Avik127/RDNT/website/img/slideshow/477grp18.jpg

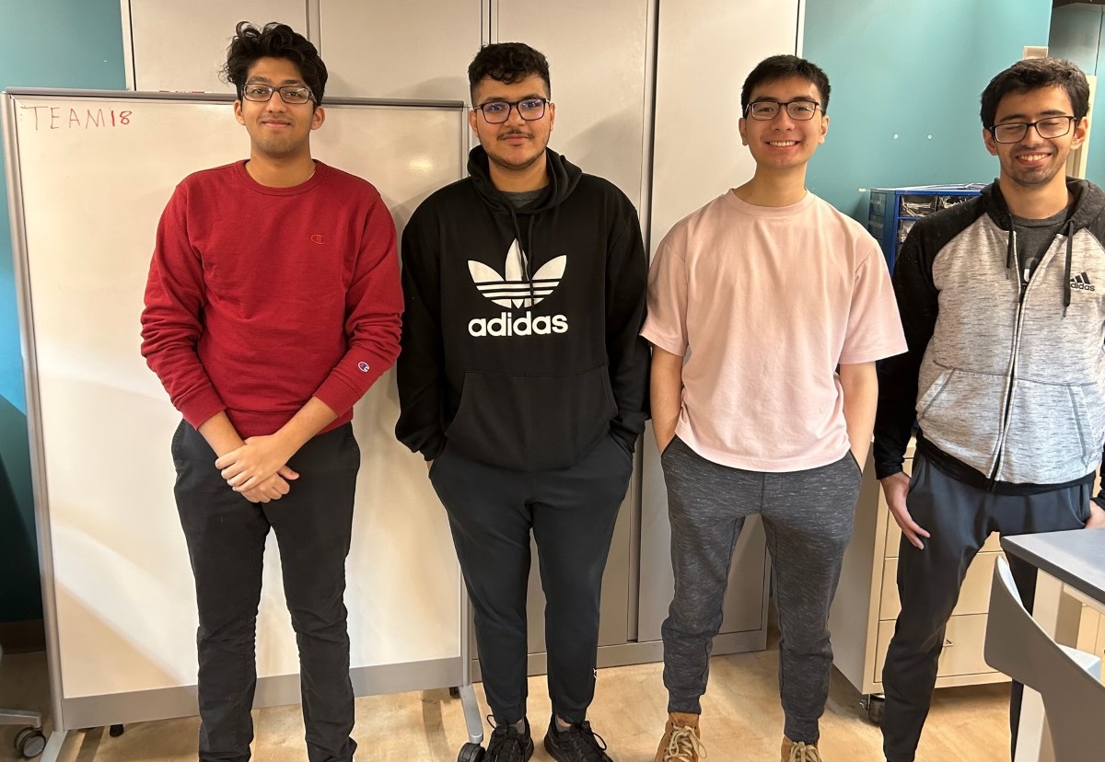
website/img/slideshow/477grp18.jpg
