Avik127/RDNT/website/img/slideshow/team_at_work.jpg

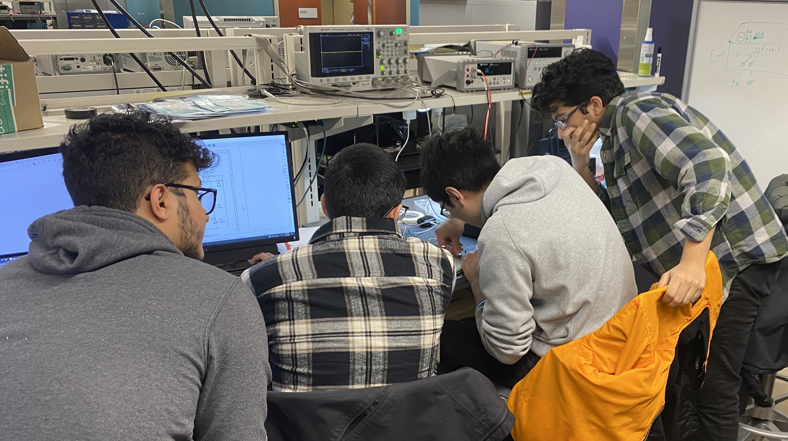
website/img/slideshow/team_at_work.jpg
