Avik127/RDNT/website/img/slideshow/team_done.jpg

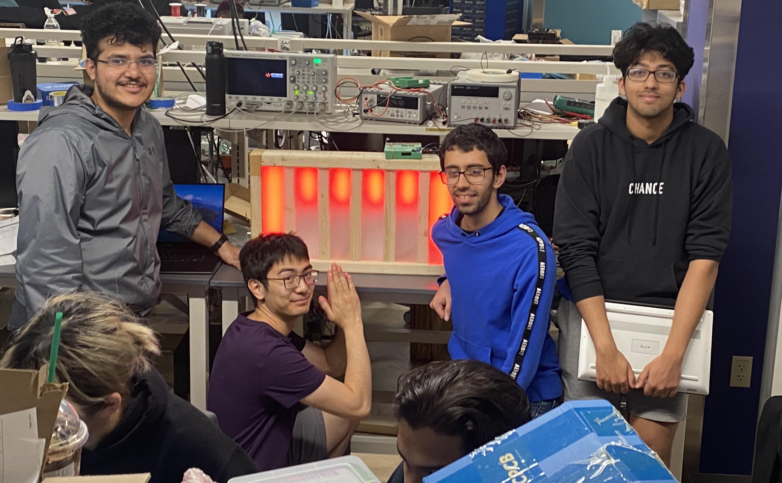
website/img/slideshow/team_done.jpg
