Avik127/RDNT/website/Team/img/avik.jpg

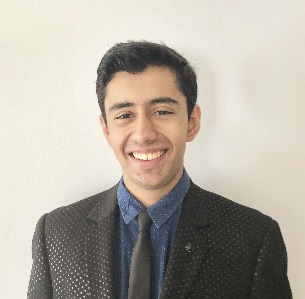
website/Team/img/avik.jpg
