Avik127/RDNT/website/Team/img/graeme.jpg

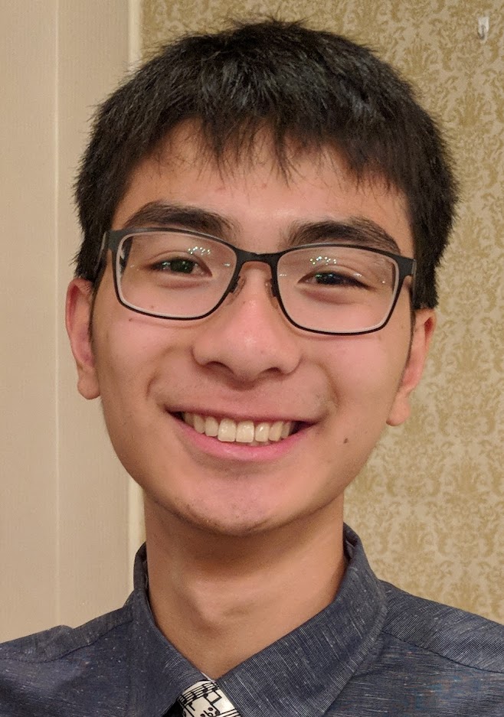
website/Team/img/graeme.jpg
