Avik127/RDNT/website/Team/progress/progress1pics/amp_voltage.jpg

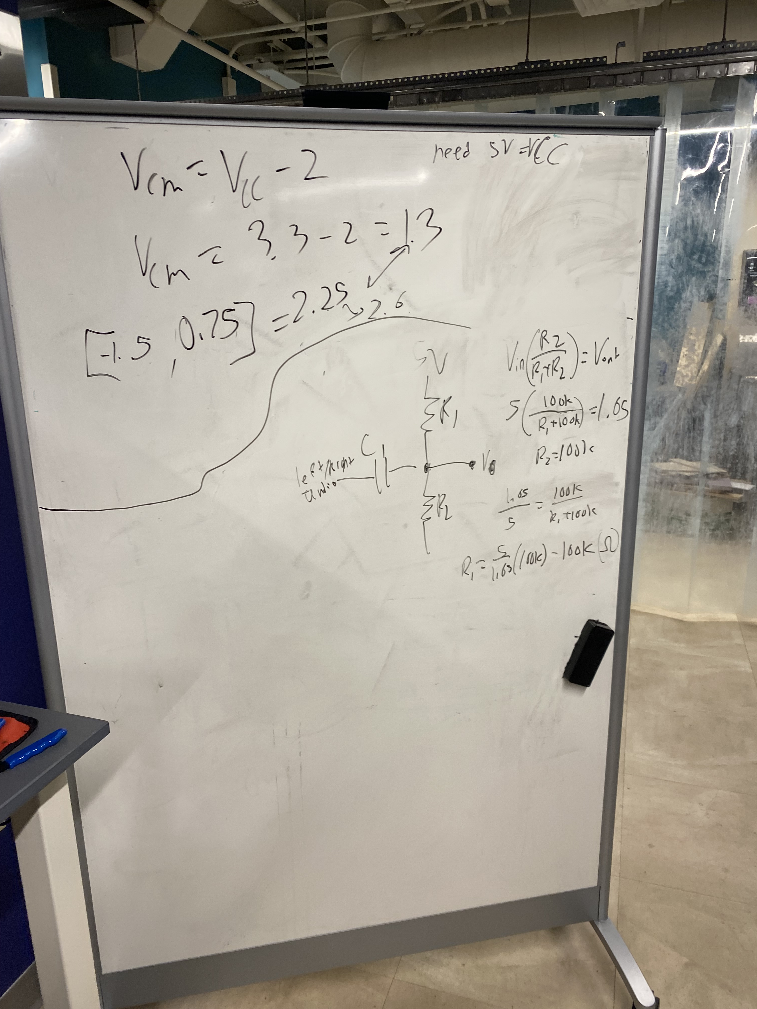
website/Team/progress/progress1pics/amp_voltage.jpg
