Avik127/RDNT/website/Team/progress/progress1pics/appdraft1.jpg

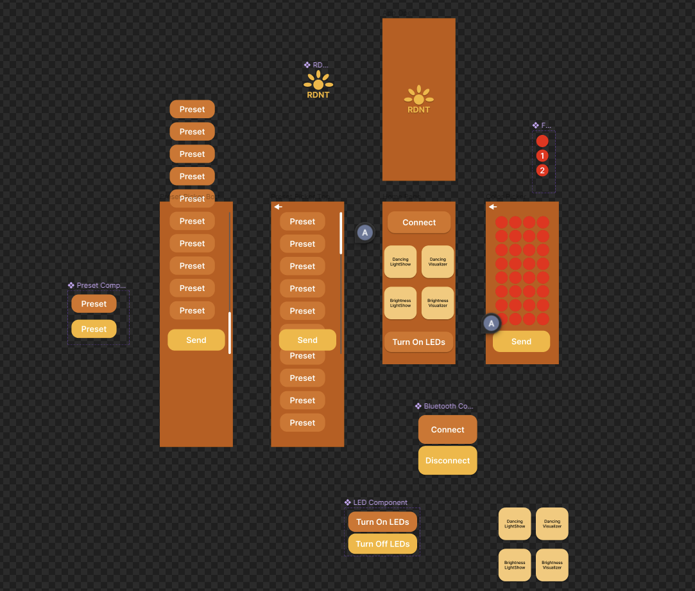
website/Team/progress/progress1pics/appdraft1.jpg
