Avik127/RDNT/website/Team/progress/progress1pics/AUX_circuit.jpg

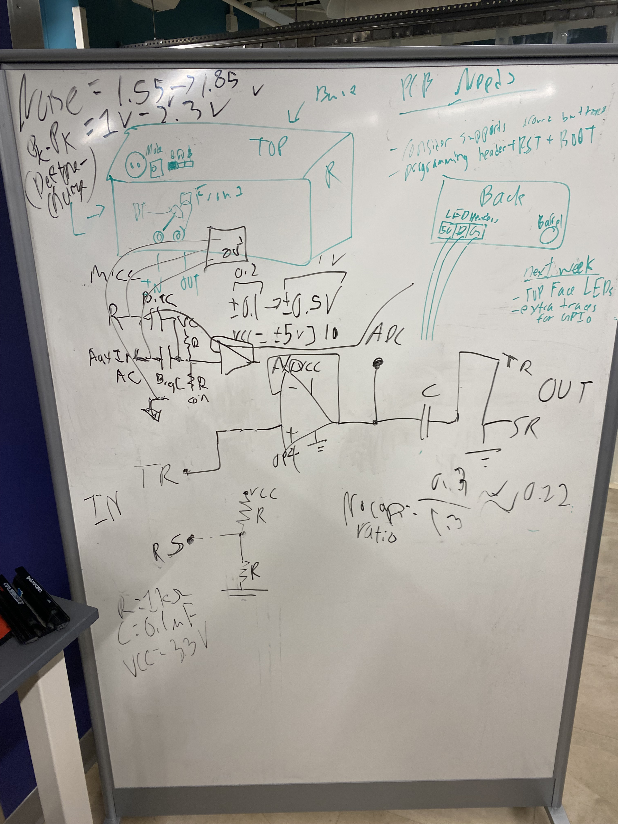
website/Team/progress/progress1pics/AUX_circuit.jpg
