Avik127/RDNT/website/Team/progress/progress1pics/desmoscalc.jpg

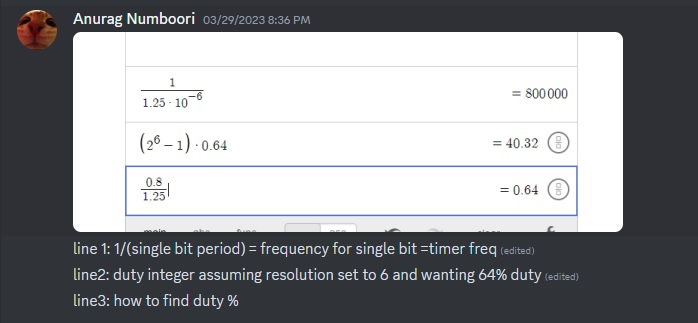
website/Team/progress/progress1pics/desmoscalc.jpg
