Avik127/RDNT/website/Team/progress/progress1pics/flashing.gif

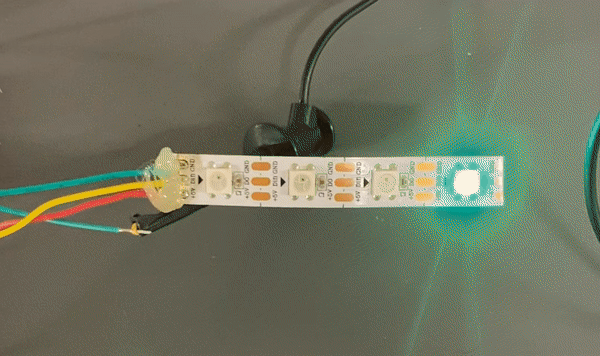
website/Team/progress/progress1pics/flashing.gif
