Avik127/RDNT/website/Team/progress/progress1pics/gain10.jpg

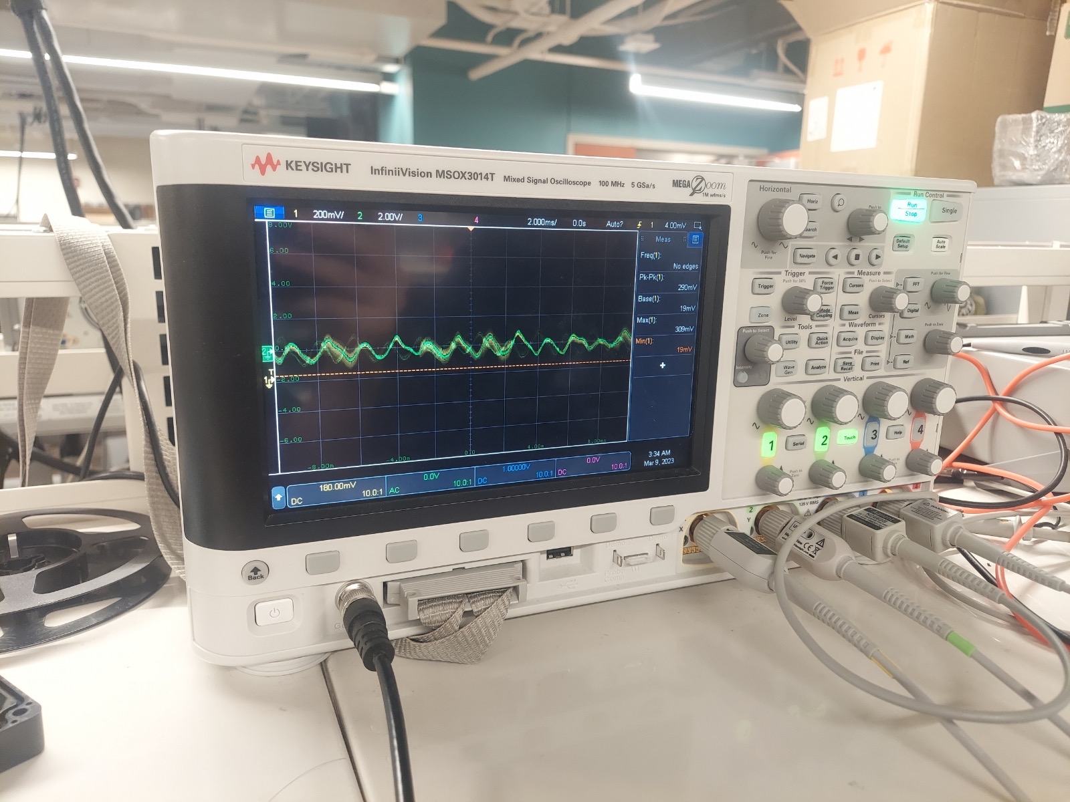
website/Team/progress/progress1pics/gain10.jpg
