Avik127/RDNT/website/Team/progress/progress1pics/GaussianDistribution.png

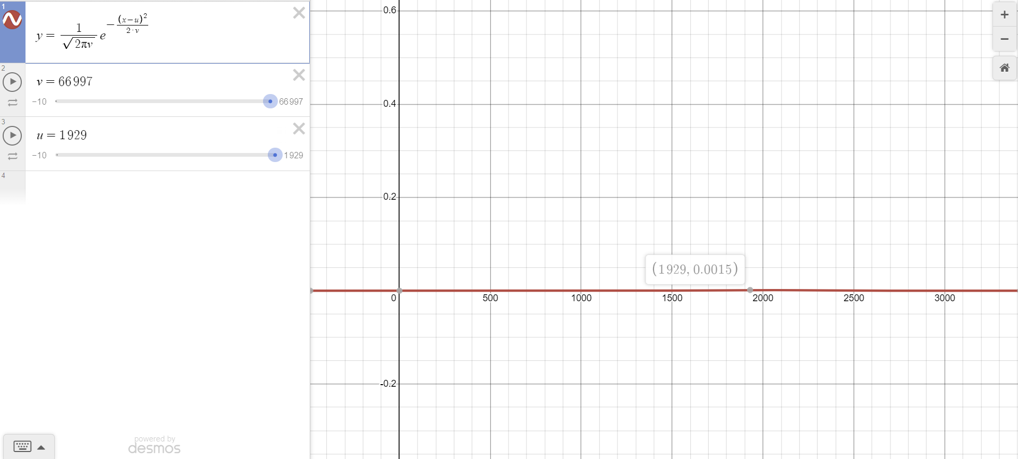
website/Team/progress/progress1pics/GaussianDistribution.png
