Avik127/RDNT/website/Team/progress/progress1pics/glue.jpg

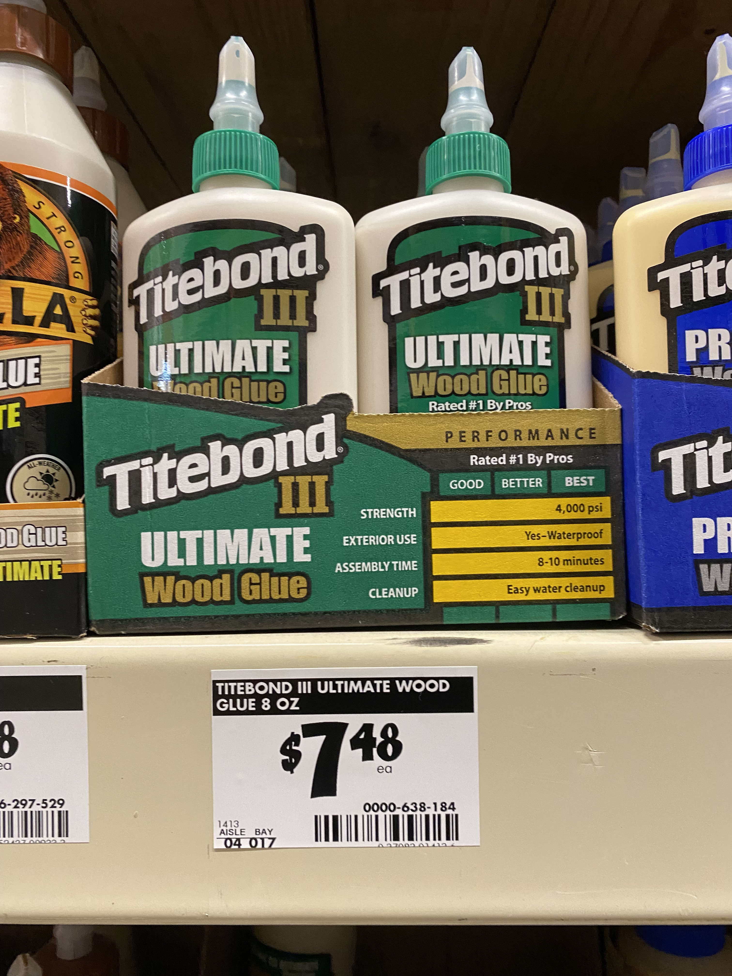
website/Team/progress/progress1pics/glue.jpg
