Avik127/RDNT/website/Team/progress/progress1pics/gpio.jpg

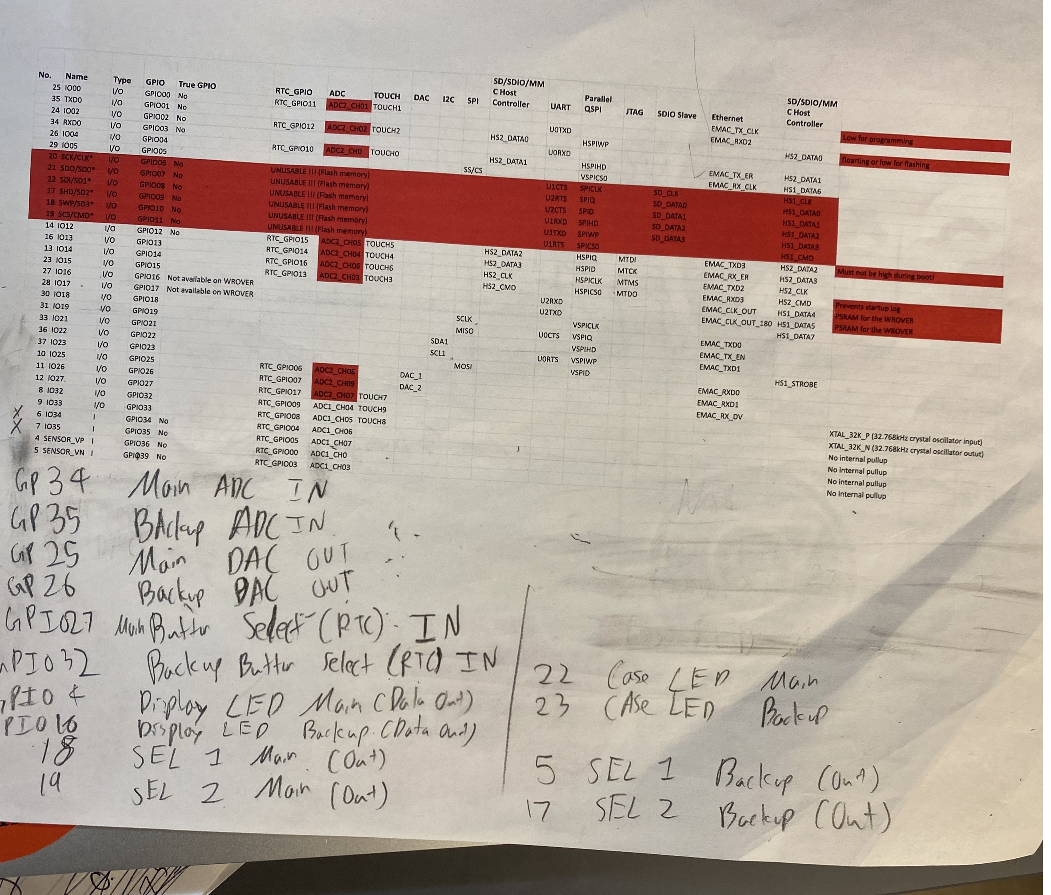
website/Team/progress/progress1pics/gpio.jpg
