Avik127/RDNT/website/Team/progress/progress1pics/IMG_4288.jpg

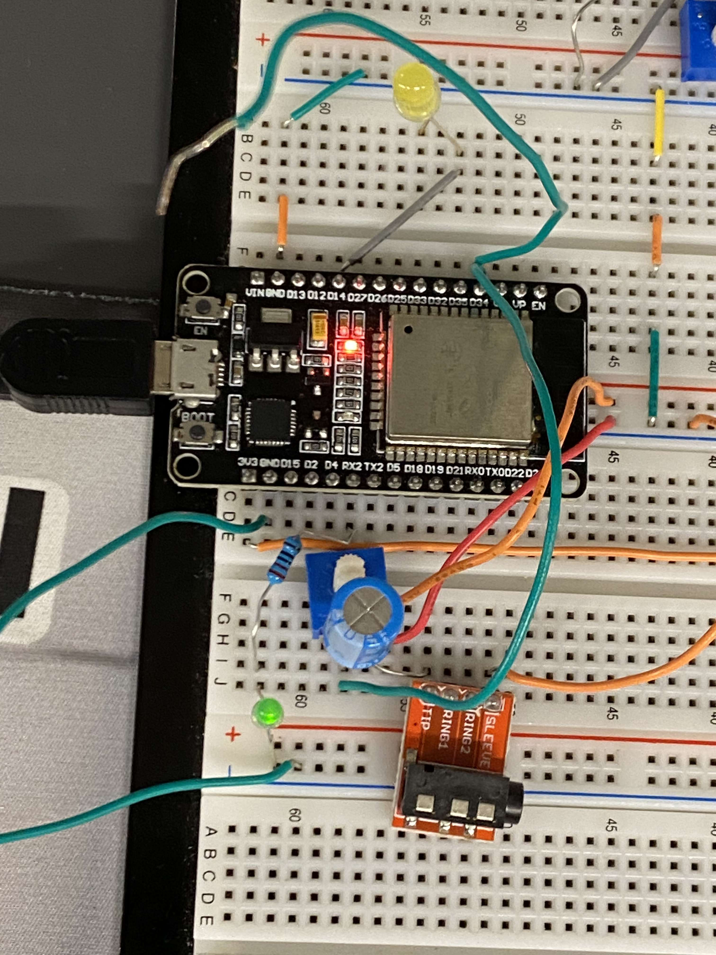
website/Team/progress/progress1pics/IMG_4288.jpg
