Avik127/RDNT/website/Team/progress/progress1pics/multi_color.jpg

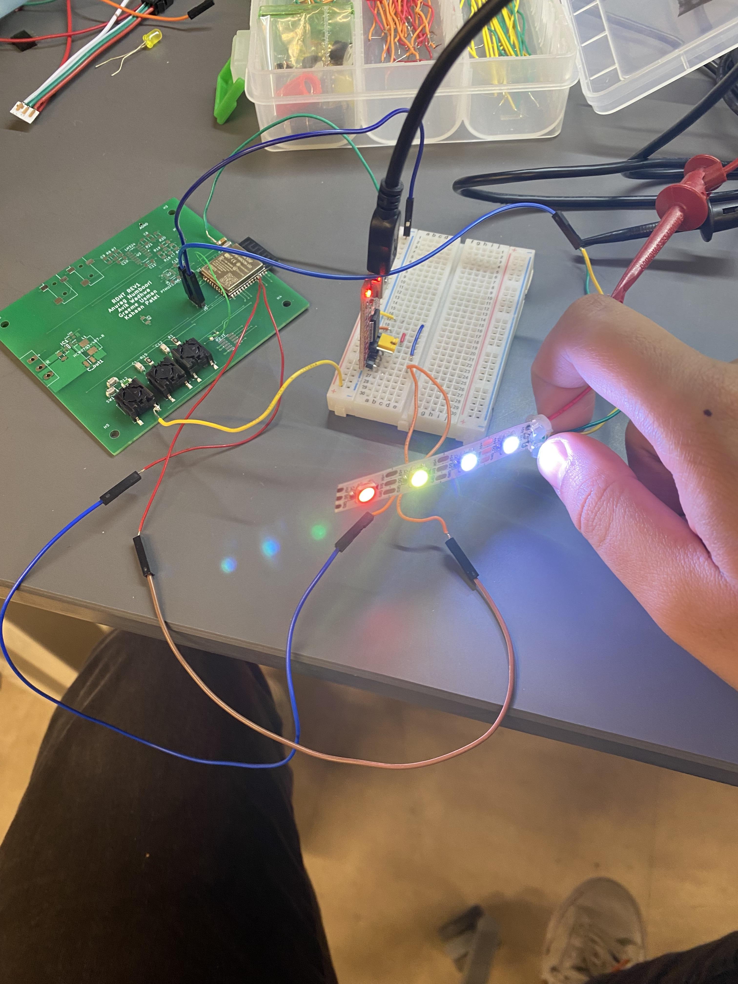
website/Team/progress/progress1pics/multi_color.jpg
