Avik127/RDNT/website/Team/progress/progress1pics/pcb_white.jpg

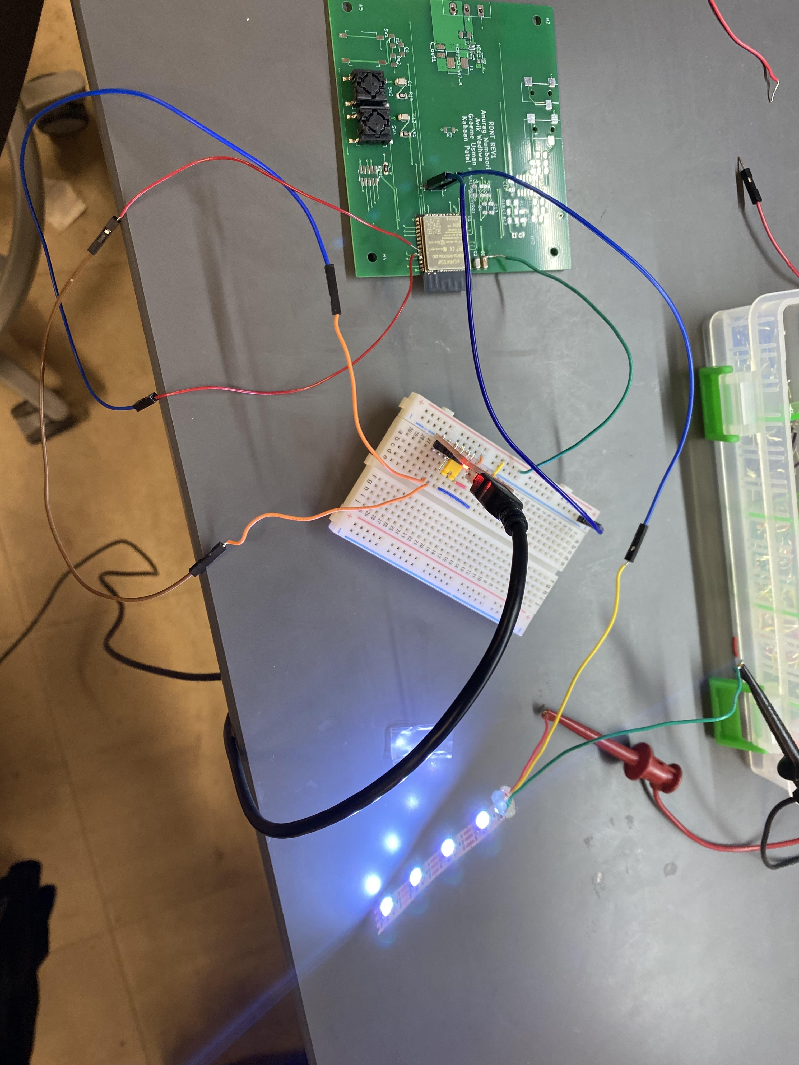
website/Team/progress/progress1pics/pcb_white.jpg
