Avik127/RDNT/website/Team/progress/progress1pics/pwm.jpg

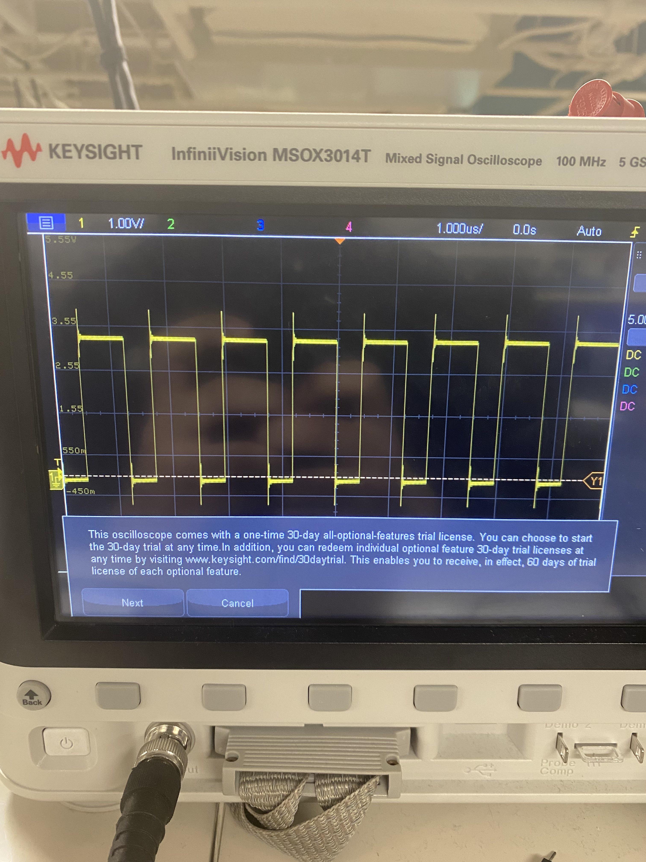
website/Team/progress/progress1pics/pwm.jpg
