Avik127/RDNT/website/Team/progress/progress1pics/red_flashing.gif

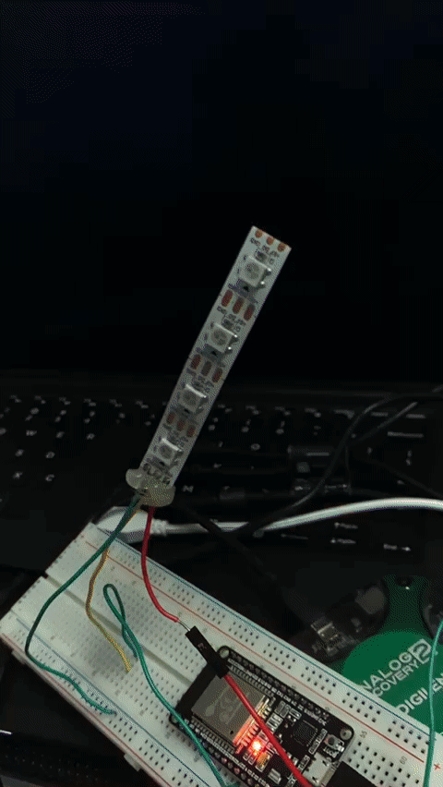
website/Team/progress/progress1pics/red_flashing.gif
