Avik127/RDNT/website/Team/progress/progress1pics/stain.jpg

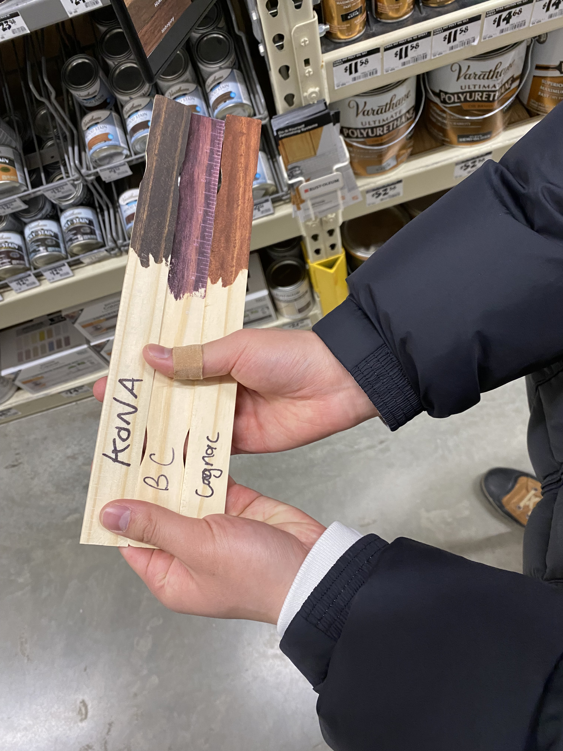
website/Team/progress/progress1pics/stain.jpg
