Avik127/RDNT/website/Team/progress/progress1pics/varnish.jpg

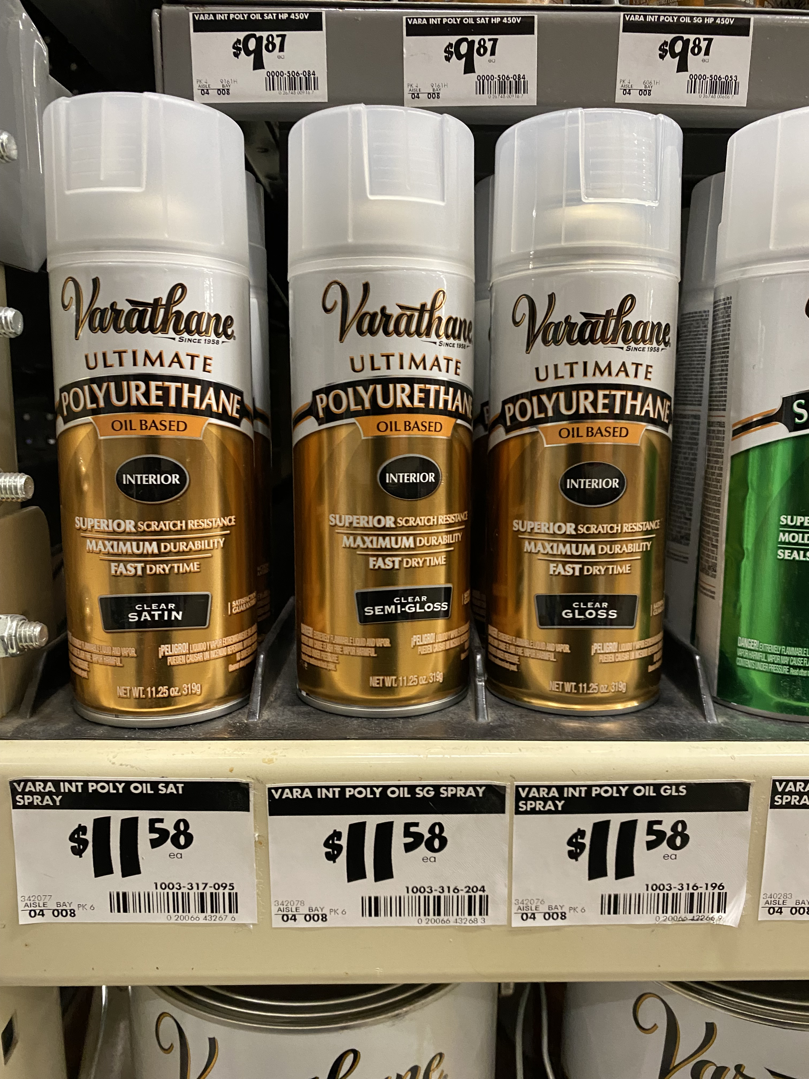
website/Team/progress/progress1pics/varnish.jpg
