Avik127/RDNT/website/Team/progress/progress1pics/whitelights.jpg

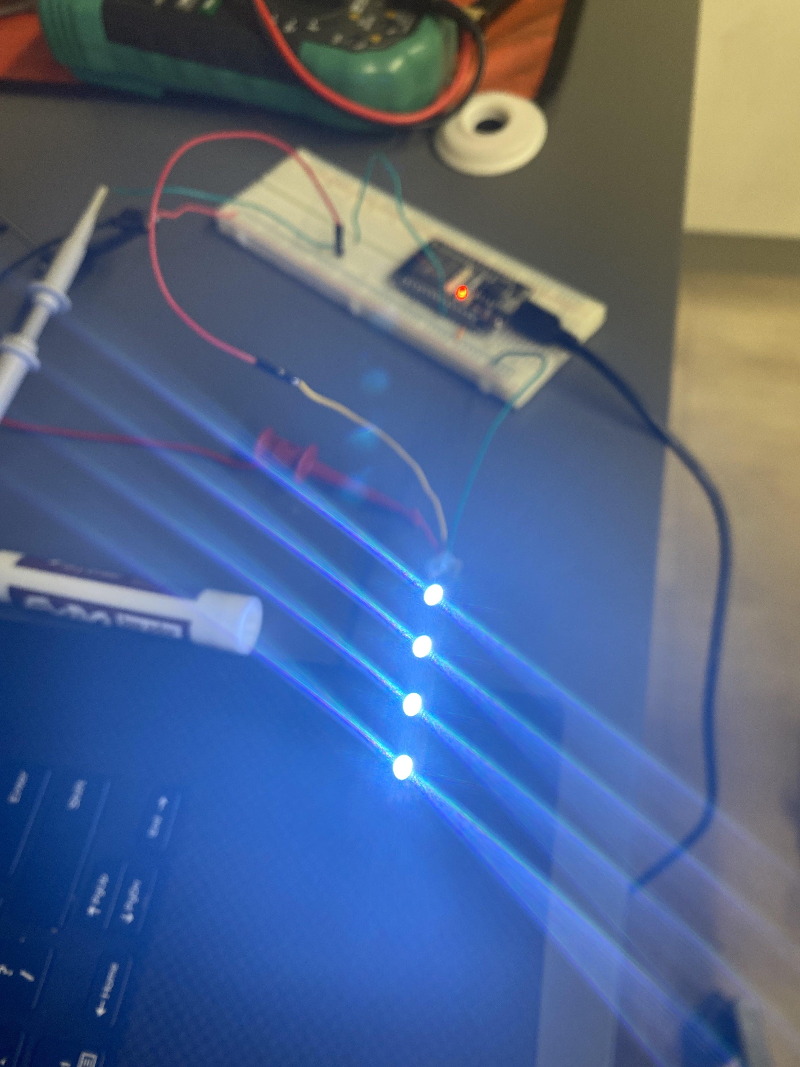
website/Team/progress/progress1pics/whitelights.jpg
