Avik127/RDNT/website/Team/progress/progress1pics/wire_awg.jpg

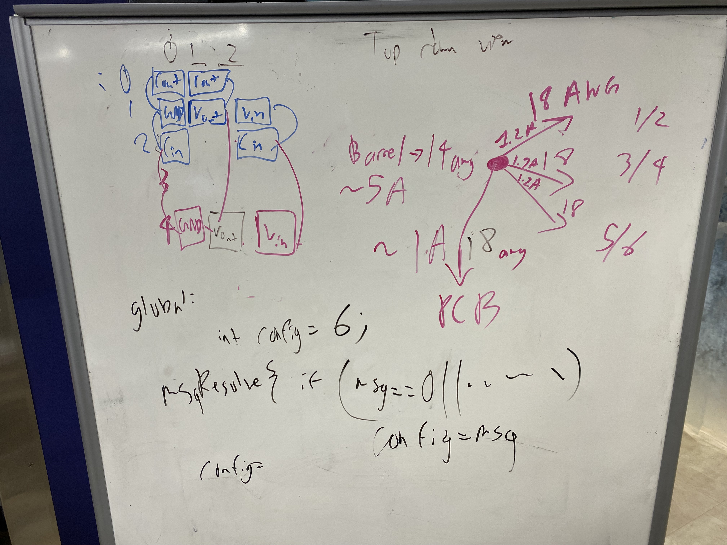
website/Team/progress/progress1pics/wire_awg.jpg
