Avik127/RDNT/website/Team/progress/progress1pics/wood.jpg

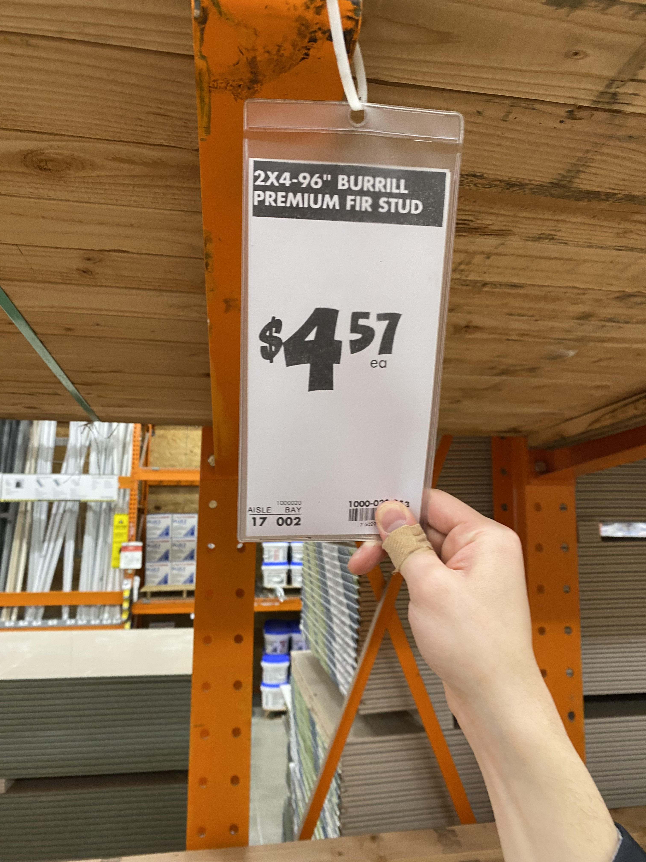
website/Team/progress/progress1pics/wood.jpg
