Avik127/RDNT/website/Team/progress/progress2pics/5V_crisis_averted.jpg

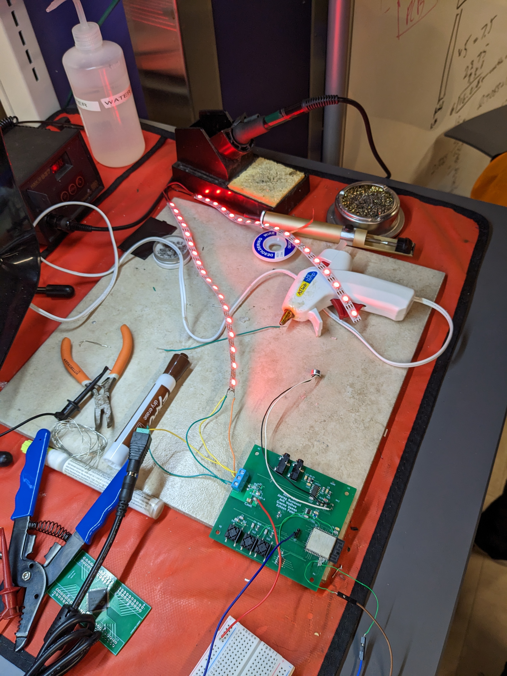
website/Team/progress/progress2pics/5V_crisis_averted.jpg
