Avik127/RDNT/website/Team/progress/progress2pics/acrylic_frosted.jpg

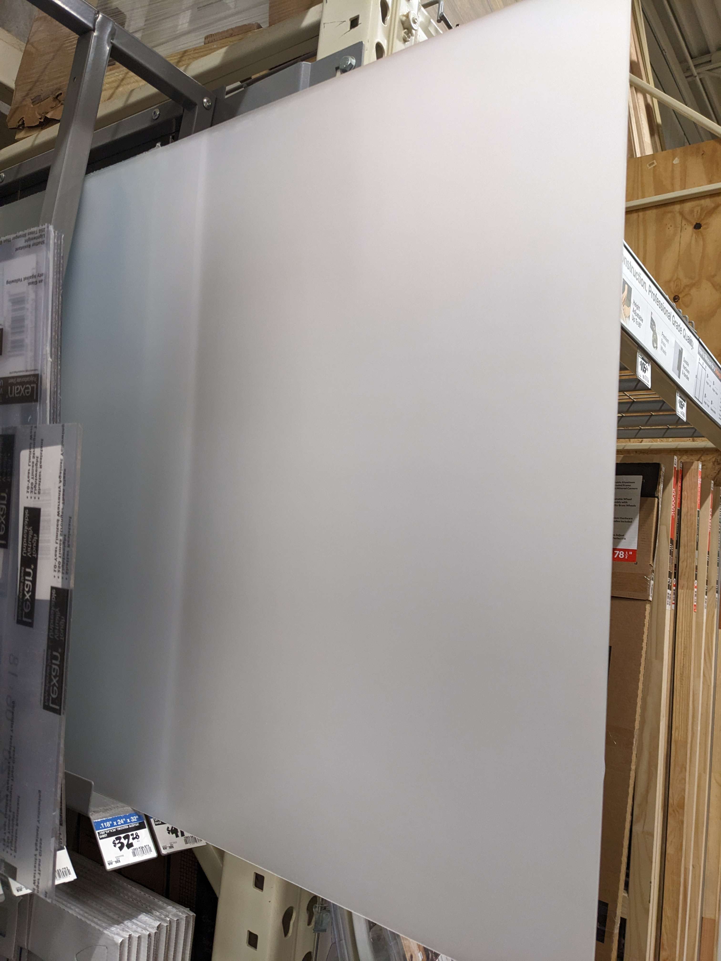
website/Team/progress/progress2pics/acrylic_frosted.jpg
