Avik127/RDNT/website/Team/progress/progress2pics/acrylic_pricetag.jpg

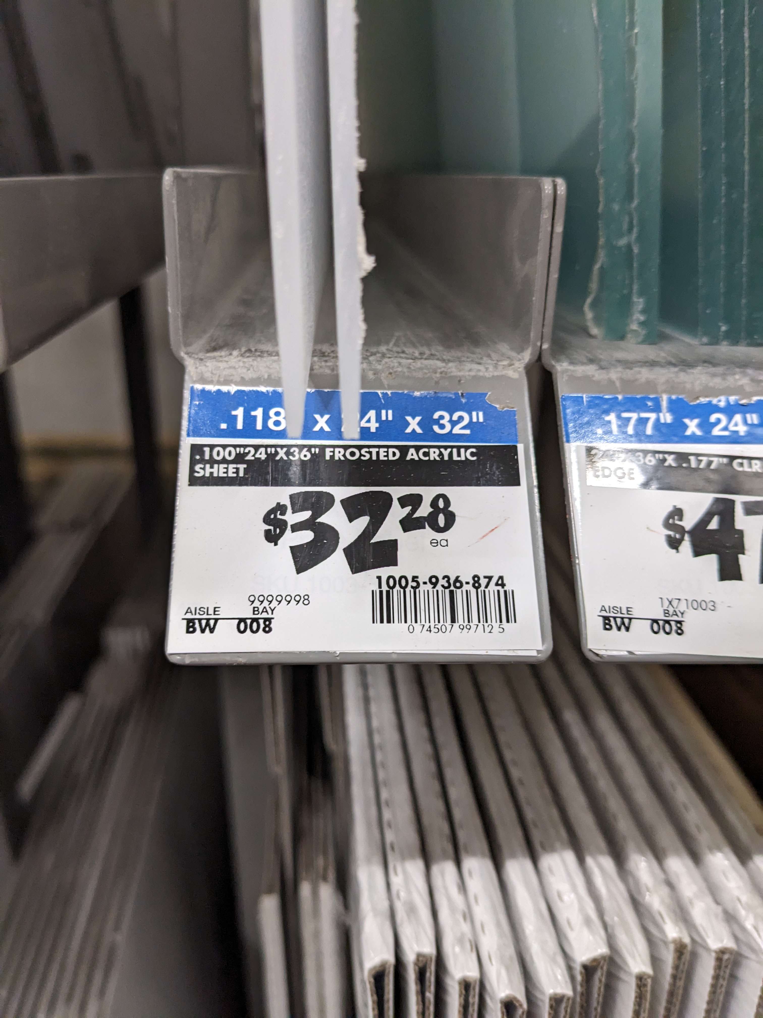
website/Team/progress/progress2pics/acrylic_pricetag.jpg
