Avik127/RDNT/website/Team/progress/progress2pics/AD2_wavegen.jpg

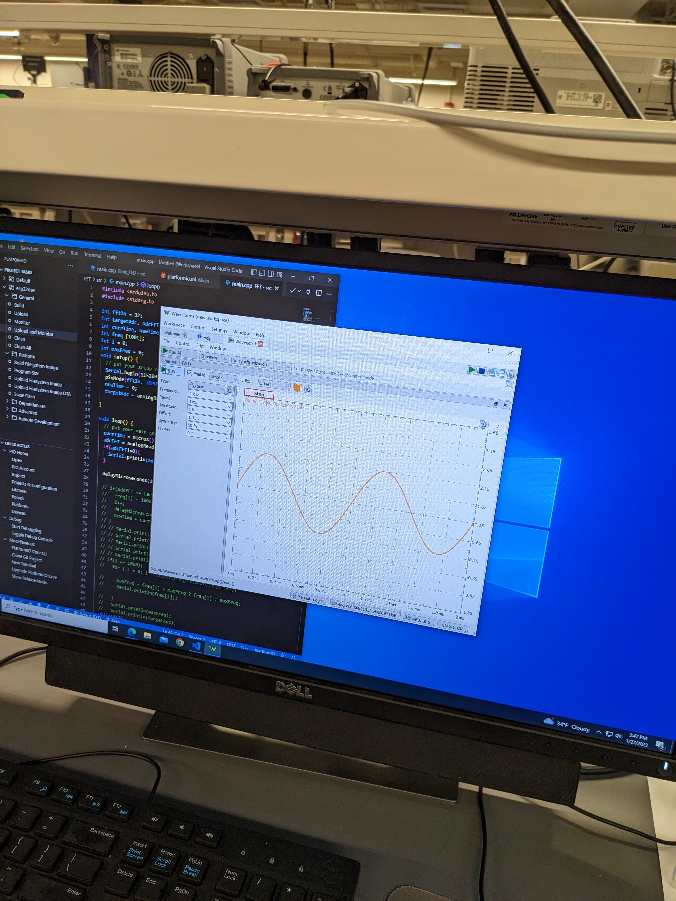
website/Team/progress/progress2pics/AD2_wavegen.jpg
