Avik127/RDNT/website/Team/progress/progress2pics/anu_work.jpg

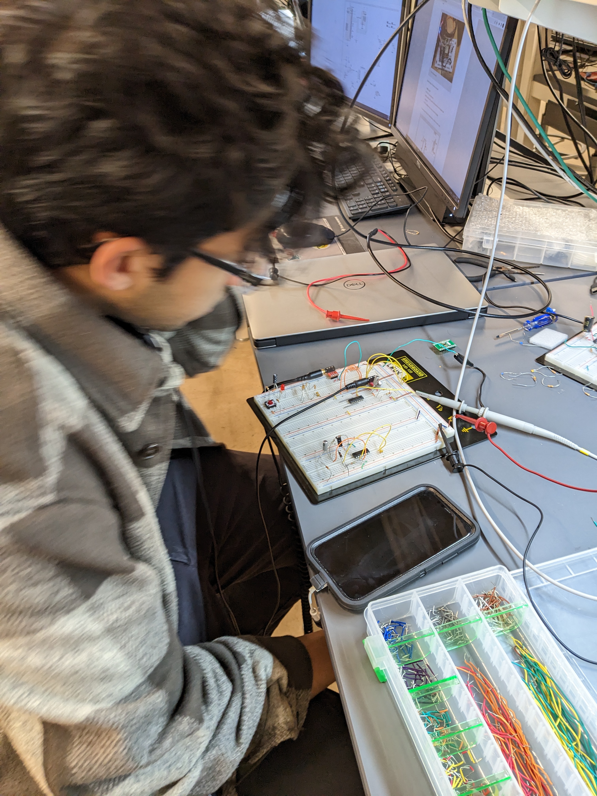
website/Team/progress/progress2pics/anu_work.jpg
