Avik127/RDNT/website/Team/progress/progress2pics/beat_detect.png

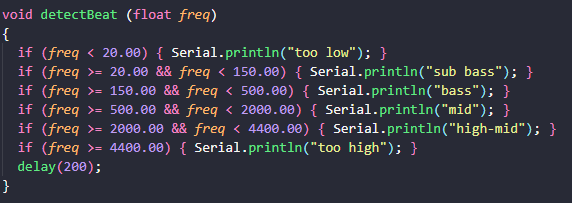
website/Team/progress/progress2pics/beat_detect.png
