Avik127/RDNT/website/Team/progress/progress2pics/button_debounced.jpg

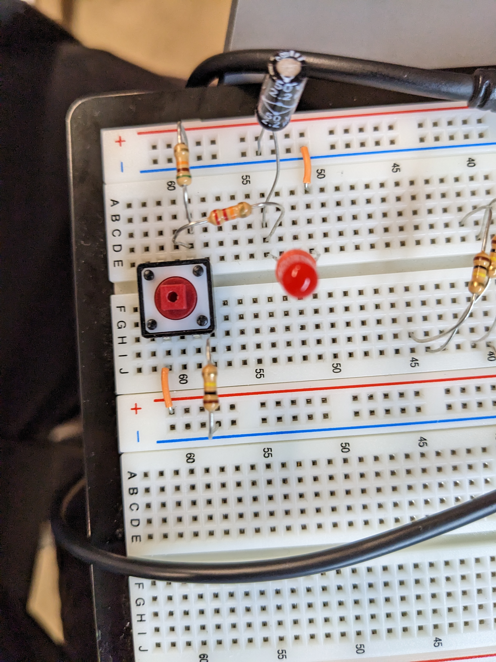
website/Team/progress/progress2pics/button_debounced.jpg
