Avik127/RDNT/website/Team/progress/progress2pics/code_3.26.png

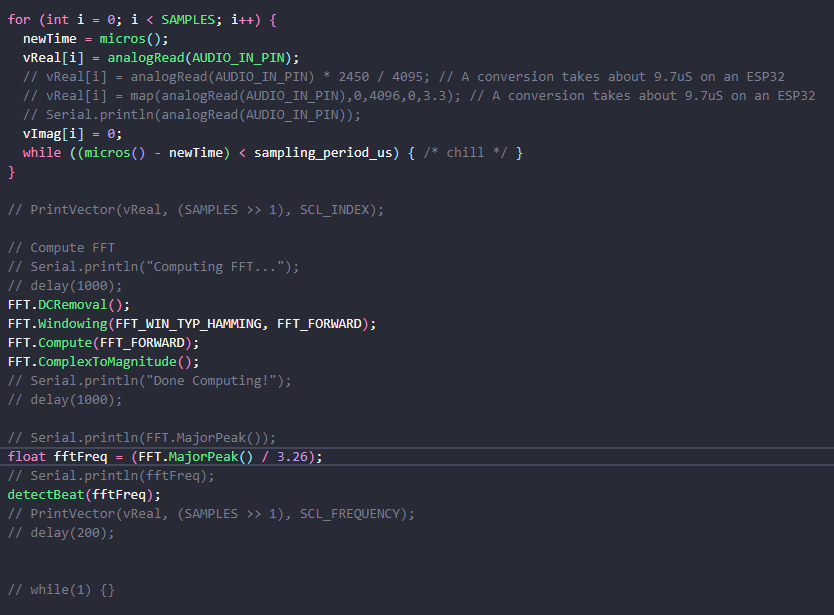
website/Team/progress/progress2pics/code_3.26.png
