Avik127/RDNT/website/Team/progress/progress2pics/epoxy.jpg

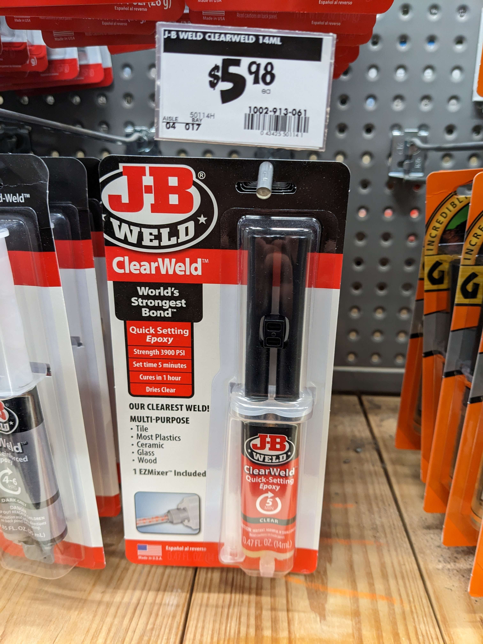
website/Team/progress/progress2pics/epoxy.jpg
