Avik127/RDNT/website/Team/progress/progress2pics/esp_time.jpg

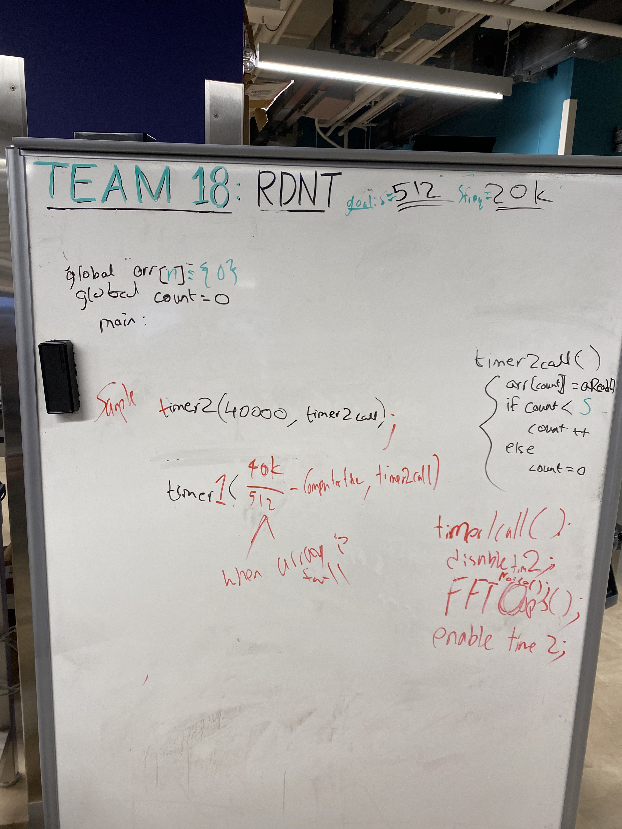
website/Team/progress/progress2pics/esp_time.jpg
