Avik127/RDNT/website/Team/progress/progress2pics/frame_update_thurs.jpg

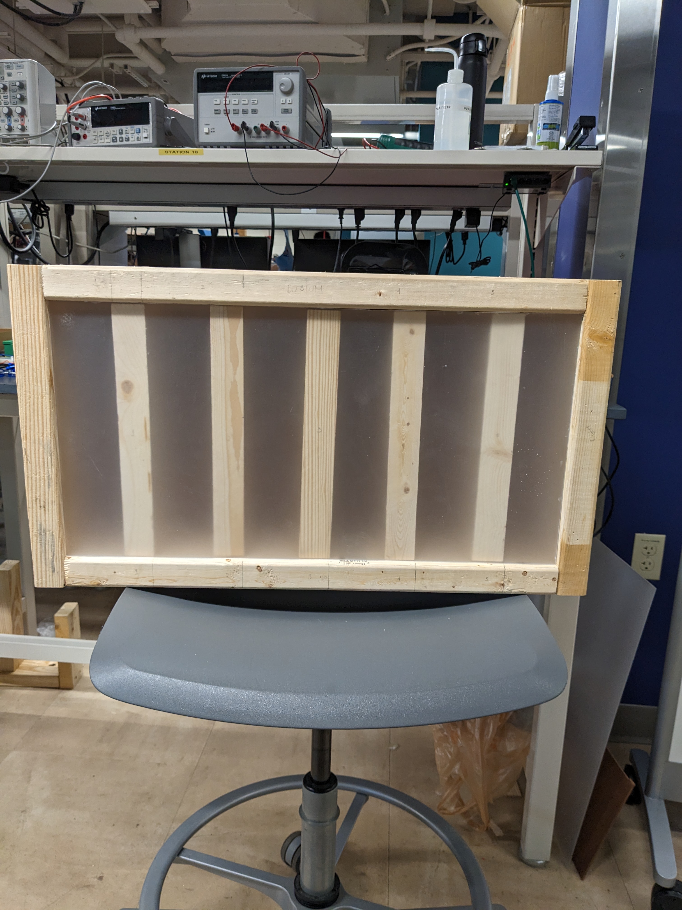
website/Team/progress/progress2pics/frame_update_thurs.jpg
