Avik127/RDNT/website/Team/progress/progress2pics/frame_update_wed.jpg

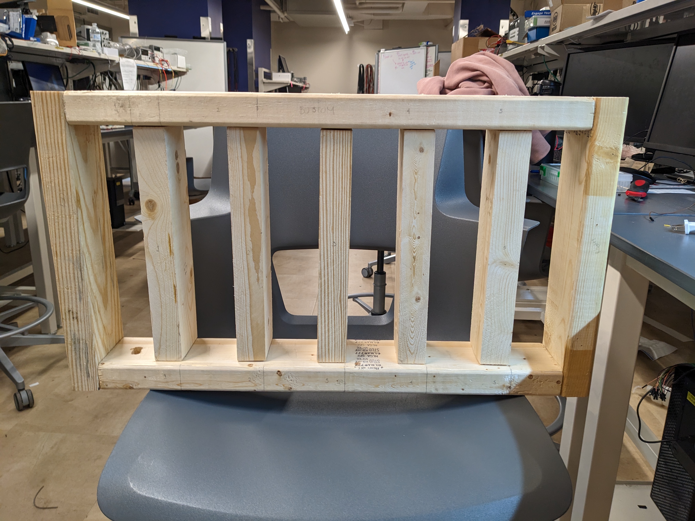
website/Team/progress/progress2pics/frame_update_wed.jpg
