Avik127/RDNT/website/Team/progress/progress2pics/freq_association.jpg

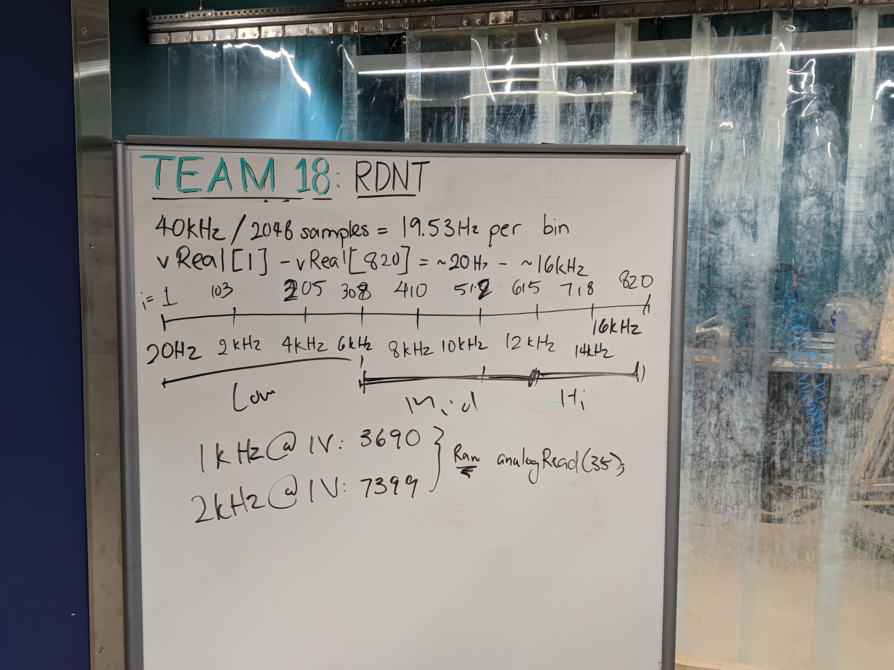
website/Team/progress/progress2pics/freq_association.jpg
