Avik127/RDNT/website/Team/progress/progress2pics/laser_cutting.jpg

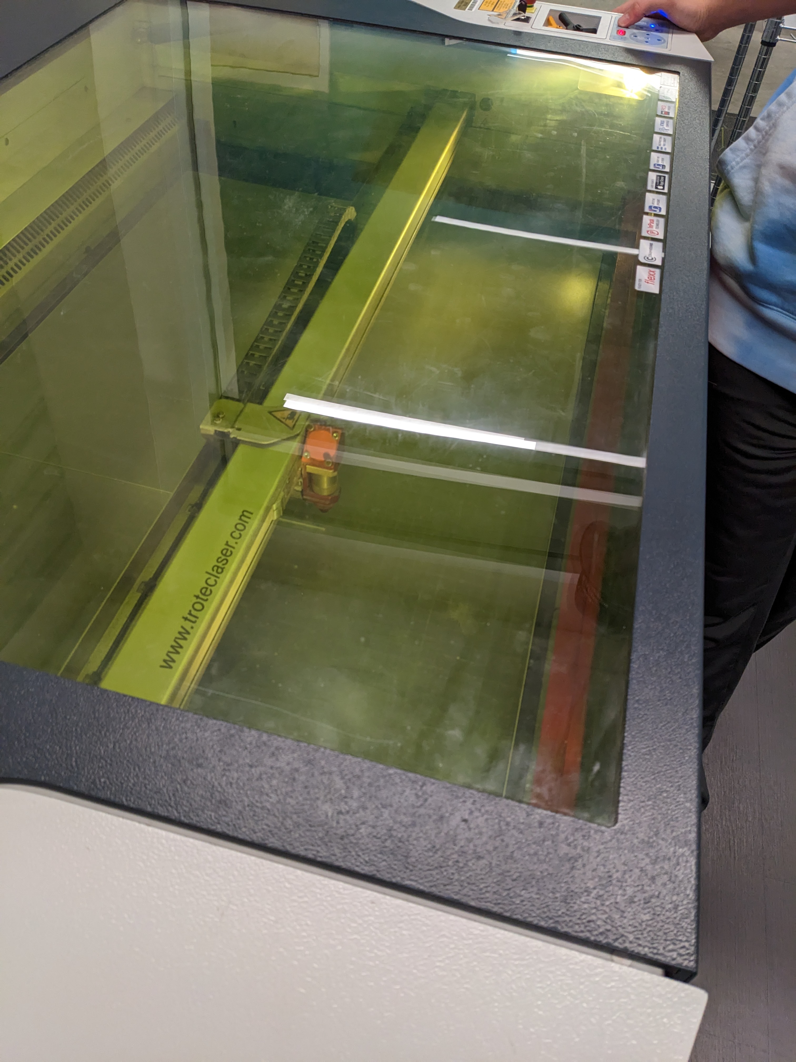
website/Team/progress/progress2pics/laser_cutting.jpg
