Avik127/RDNT/website/Team/progress/progress2pics/mic_final.jpg

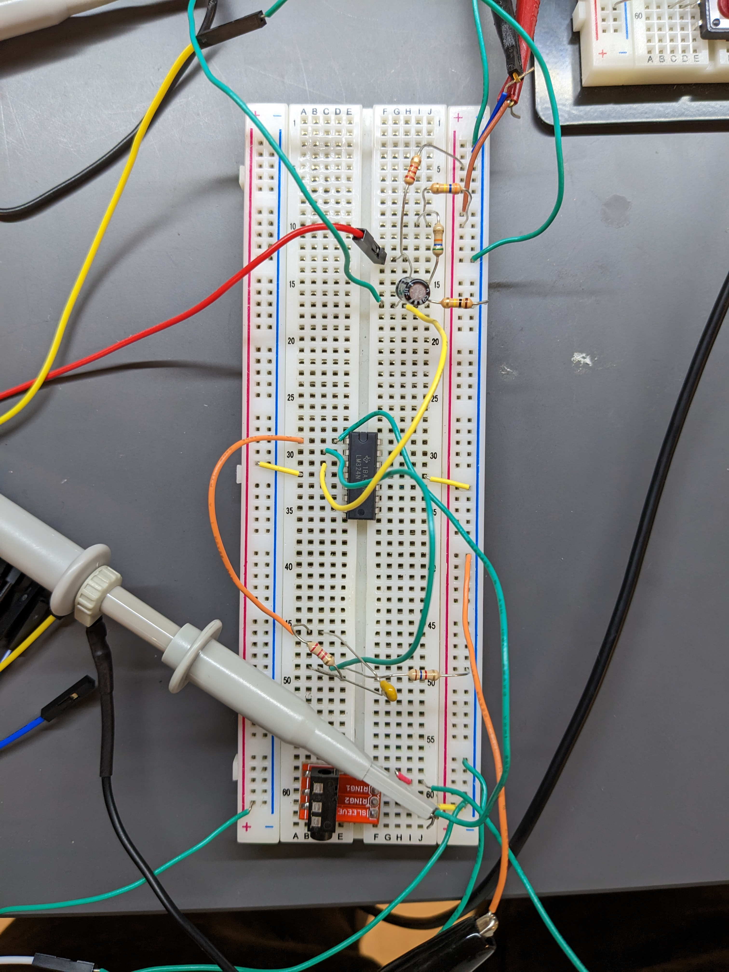
website/Team/progress/progress2pics/mic_final.jpg
