Avik127/RDNT/website/Team/progress/progress2pics/mic_output2.jpg

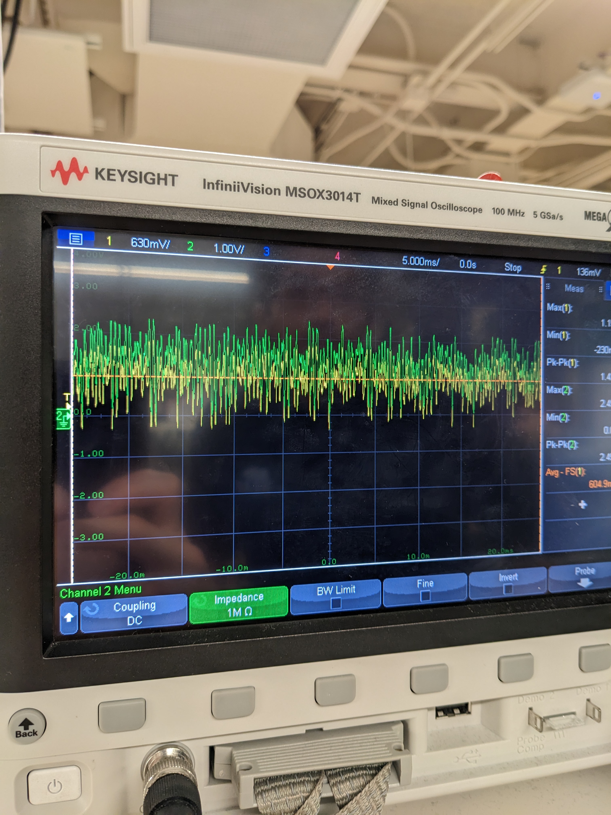
website/Team/progress/progress2pics/mic_output2.jpg
