Avik127/RDNT/website/Team/progress/progress2pics/mic_output.jpg

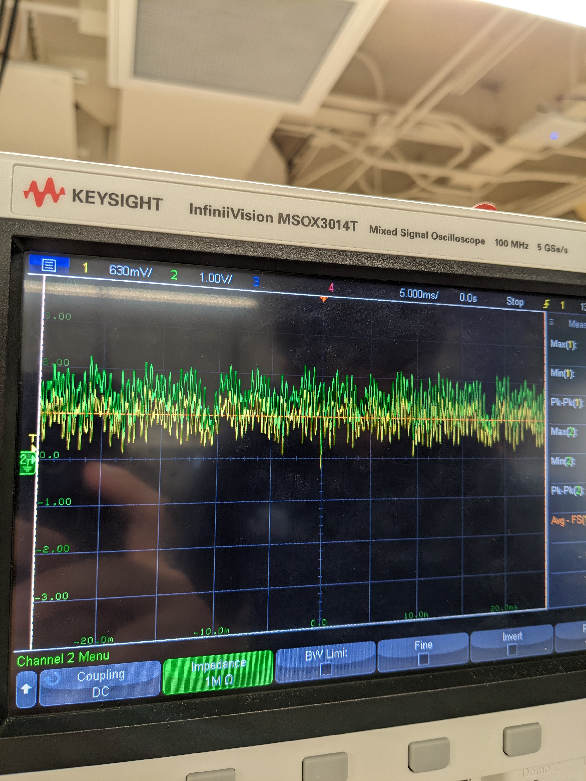
website/Team/progress/progress2pics/mic_output.jpg
