Avik127/RDNT/website/Team/progress/progress2pics/PCB_2powers.jpg

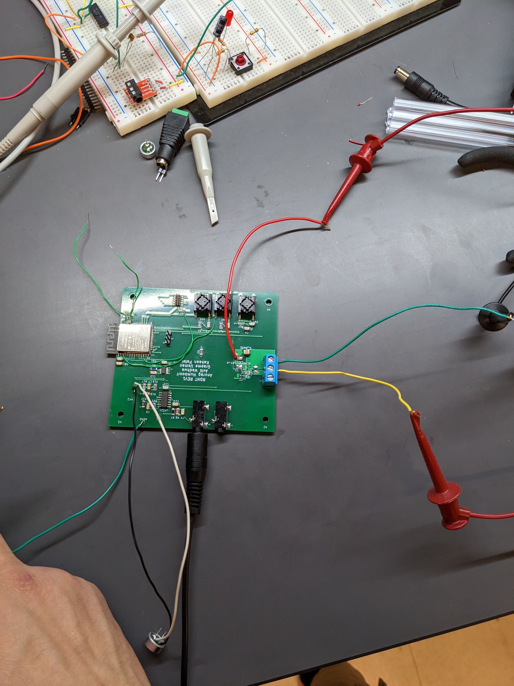
website/Team/progress/progress2pics/PCB_2powers.jpg
