Avik127/RDNT/website/Team/progress/progress2pics/PCB_aux_output.jpg

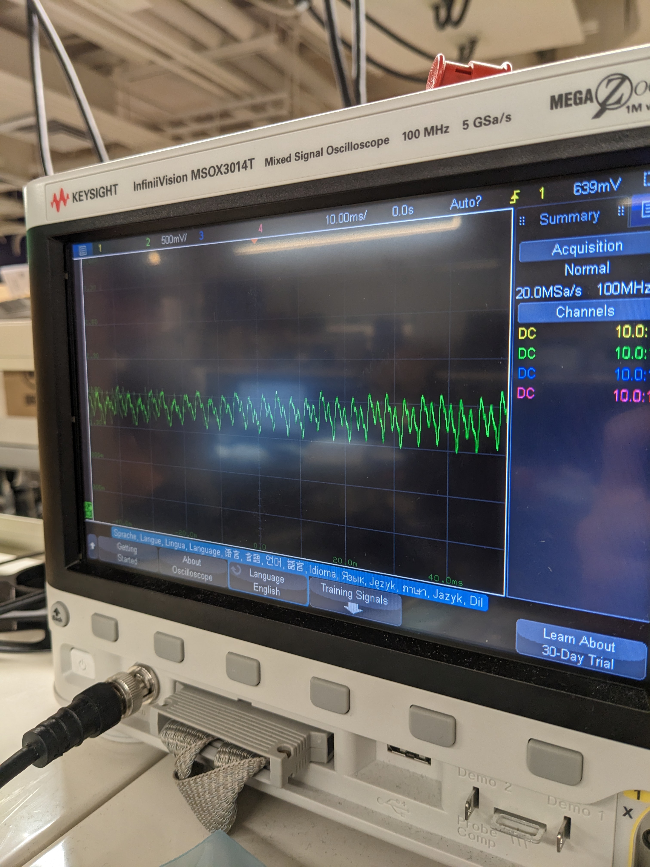
website/Team/progress/progress2pics/PCB_aux_output.jpg
