Avik127/RDNT/website/Team/progress/progress2pics/PCB_aux_output_2.jpg

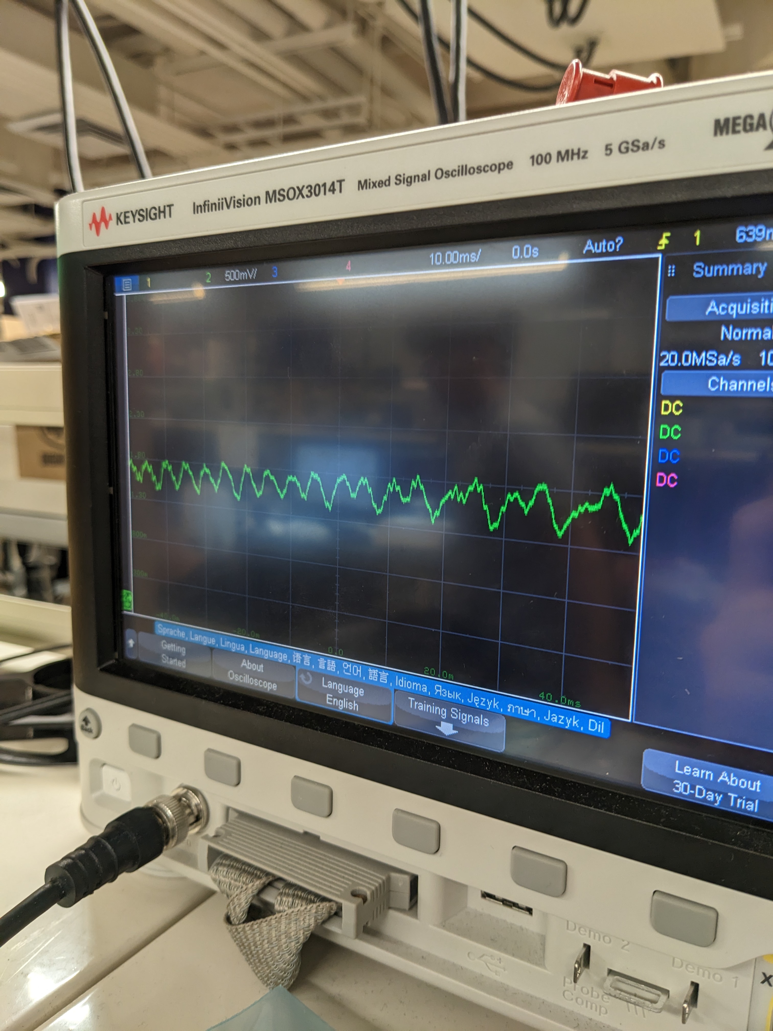
website/Team/progress/progress2pics/PCB_aux_output_2.jpg
