Avik127/RDNT/website/Team/progress/progress2pics/PCB_CPU.jpg

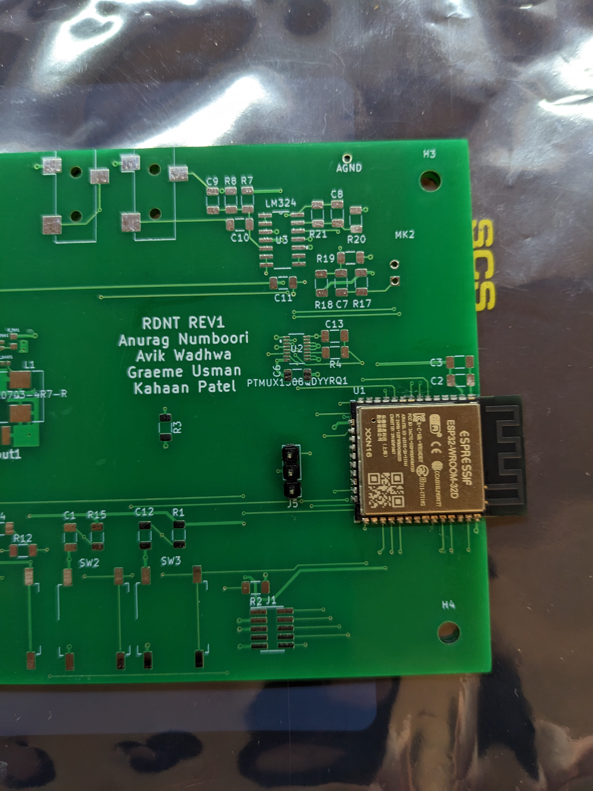
website/Team/progress/progress2pics/PCB_CPU.jpg
