Avik127/RDNT/website/Team/progress/progress2pics/PCB_CPU_buttons.jpg

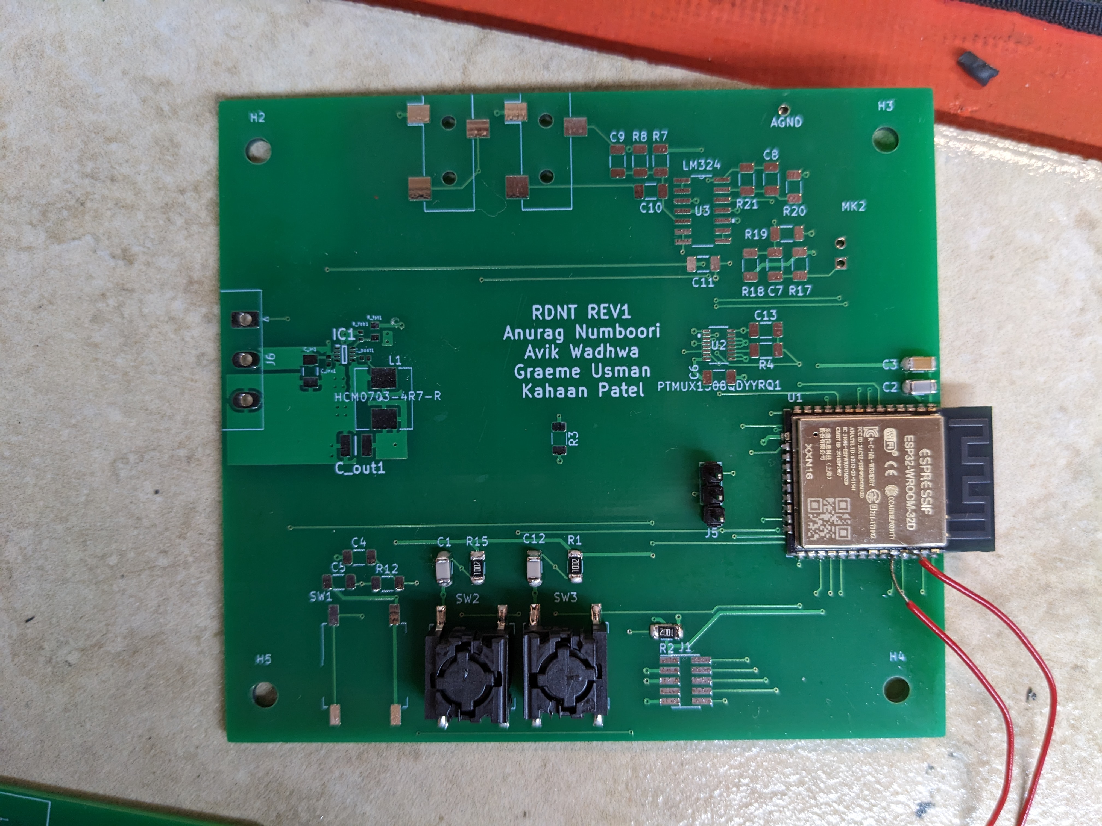
website/Team/progress/progress2pics/PCB_CPU_buttons.jpg
