Avik127/RDNT/website/Team/progress/progress2pics/PCB_full.jpg

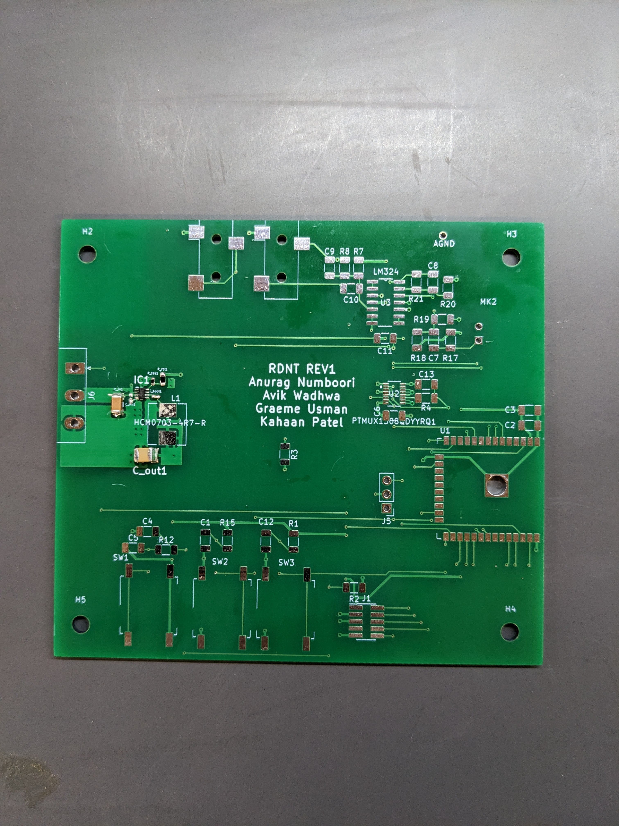
website/Team/progress/progress2pics/PCB_full.jpg
