Avik127/RDNT/website/Team/progress/progress2pics/PCB_power_circuit_complete.jpg

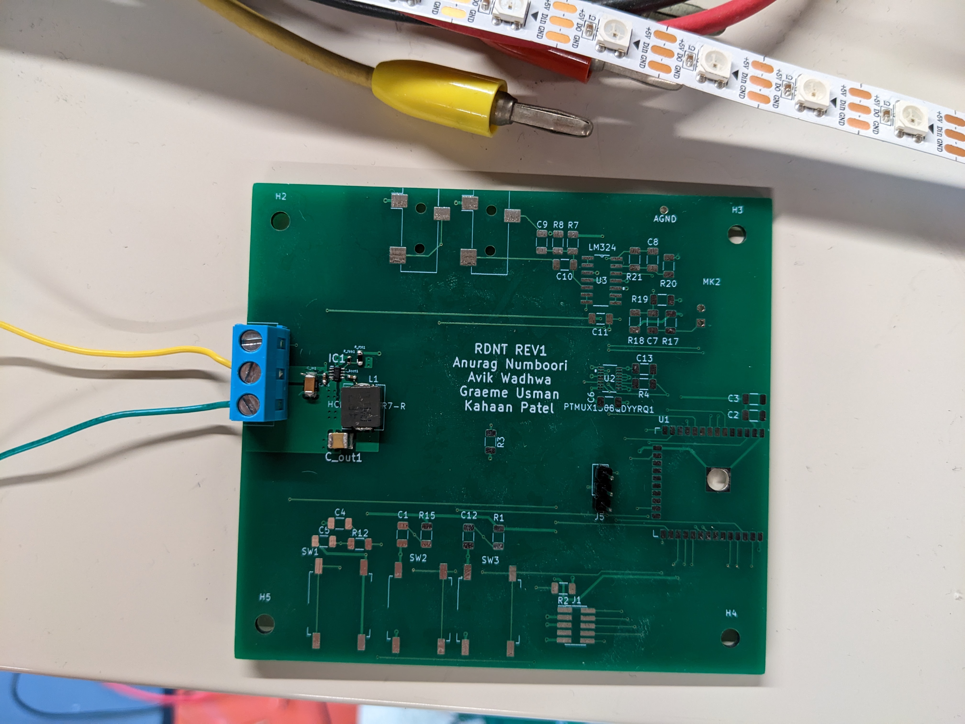
website/Team/progress/progress2pics/PCB_power_circuit_complete.jpg
