Avik127/RDNT/website/Team/progress/progress2pics/PCB_power_LDO_3.jpg

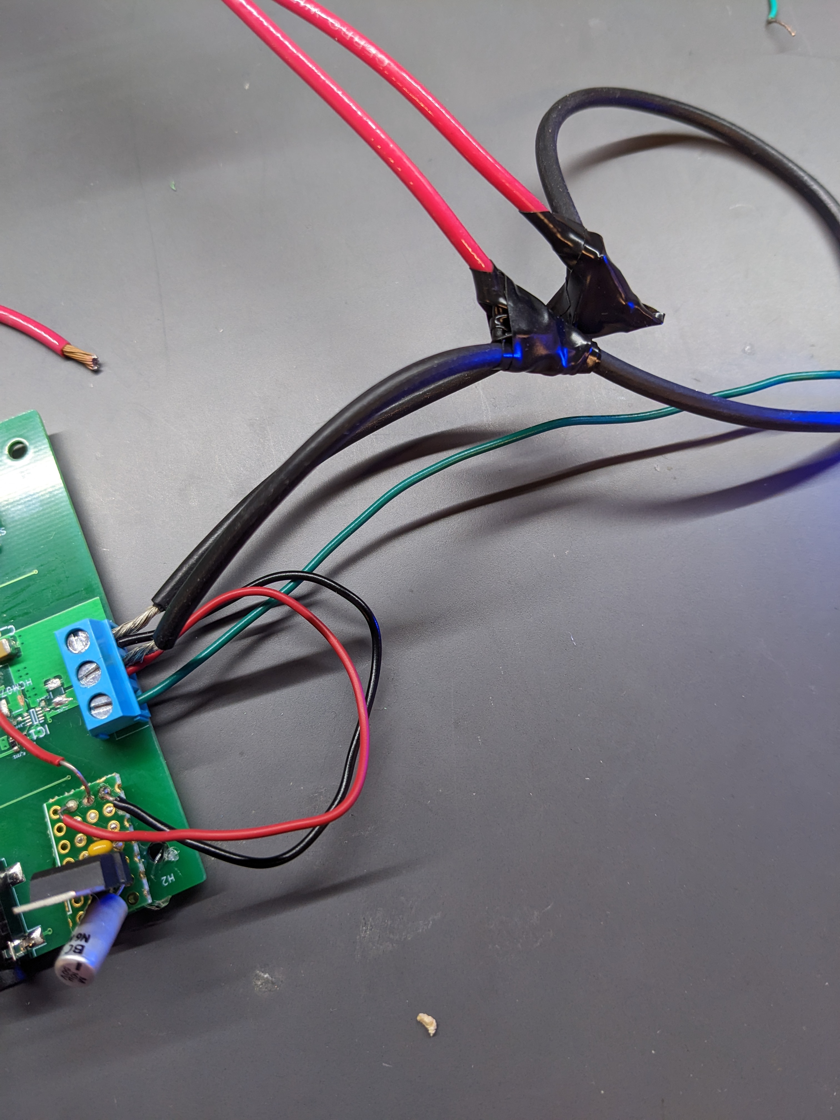
website/Team/progress/progress2pics/PCB_power_LDO_3.jpg
