Avik127/RDNT/website/Team/progress/progress2pics/PCB_progress_tues.jpg

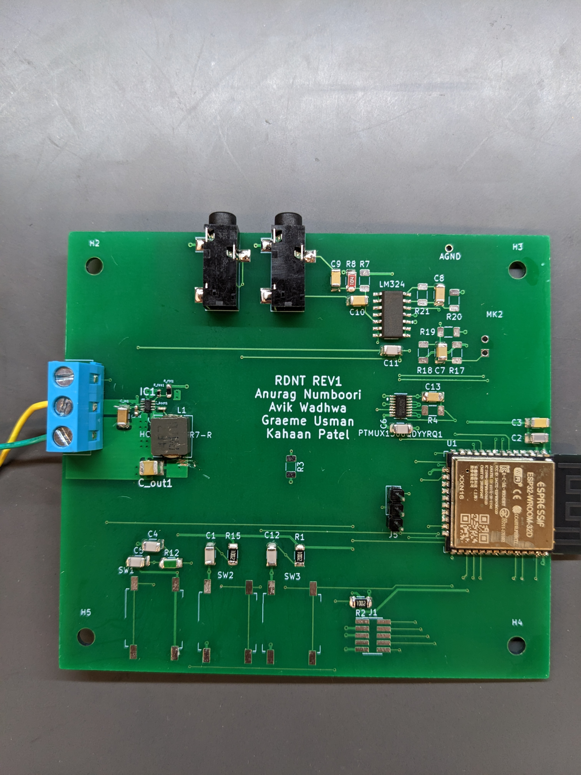
website/Team/progress/progress2pics/PCB_progress_tues.jpg
