Avik127/RDNT/website/Team/progress/progress2pics/PCB_UART.jpg

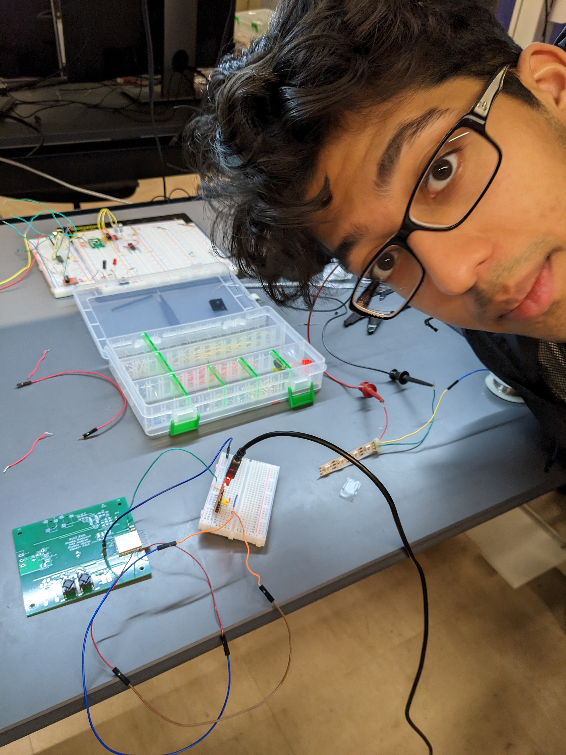
website/Team/progress/progress2pics/PCB_UART.jpg
