Avik127/RDNT/website/Team/progress/progress2pics/PCB_UART_LED_on.jpg

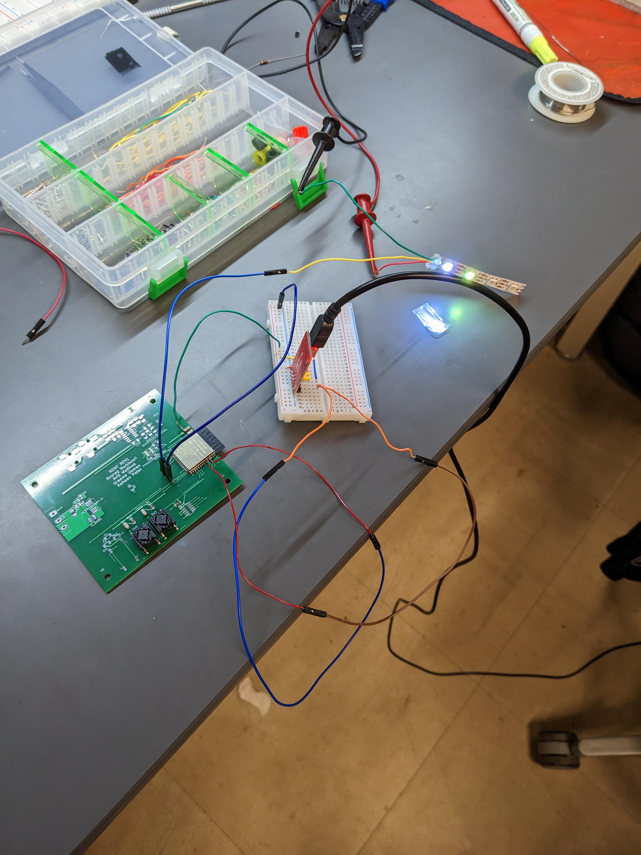
website/Team/progress/progress2pics/PCB_UART_LED_on.jpg
