Avik127/RDNT/website/Team/progress/progress2pics/pepe_silvia.jpg

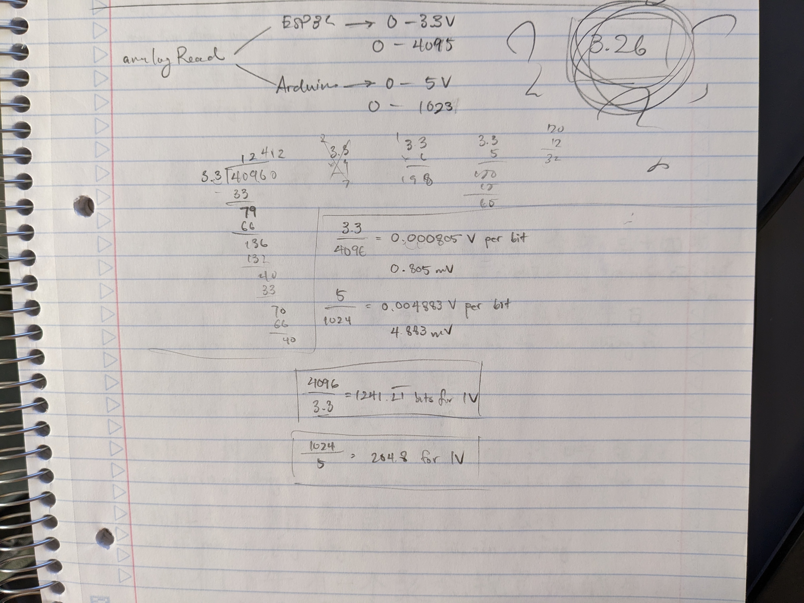
website/Team/progress/progress2pics/pepe_silvia.jpg
