Avik127/RDNT/website/Team/progress/progress2pics/planning_the_fixture.jpg

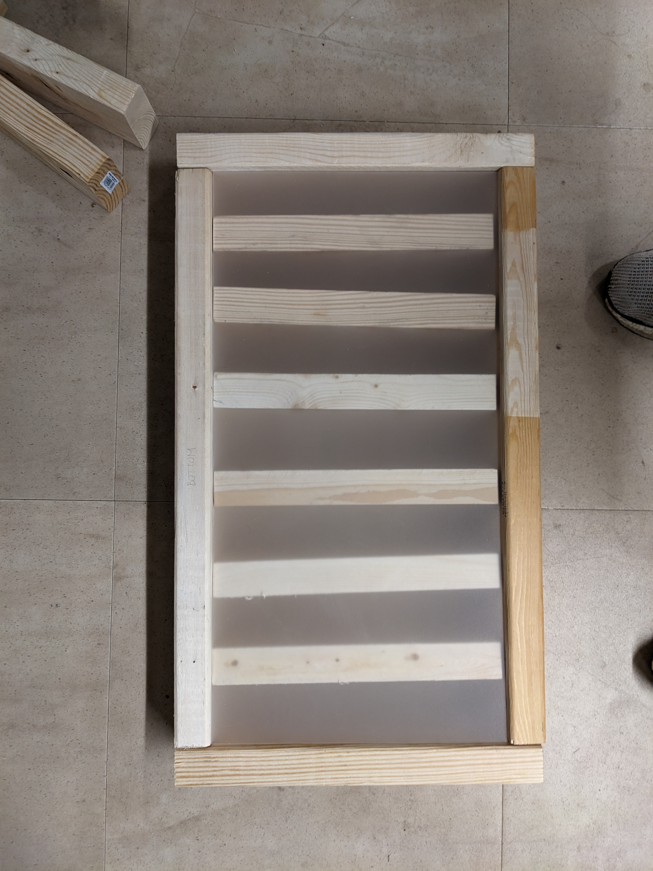
website/Team/progress/progress2pics/planning_the_fixture.jpg
