Avik127/RDNT/website/Team/progress/progress2pics/PXL_20230307_223109311.jpg

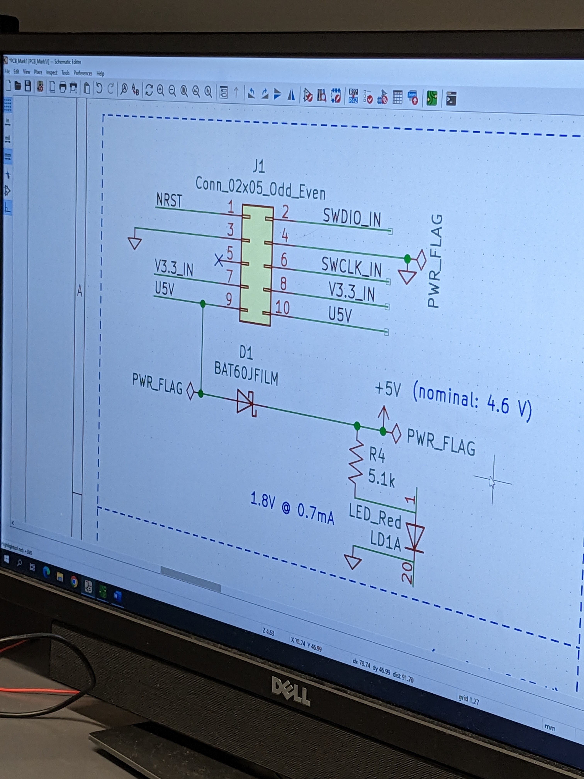
website/Team/progress/progress2pics/PXL_20230307_223109311.jpg
