Avik127/RDNT/website/Team/progress/progress2pics/stain.jpg

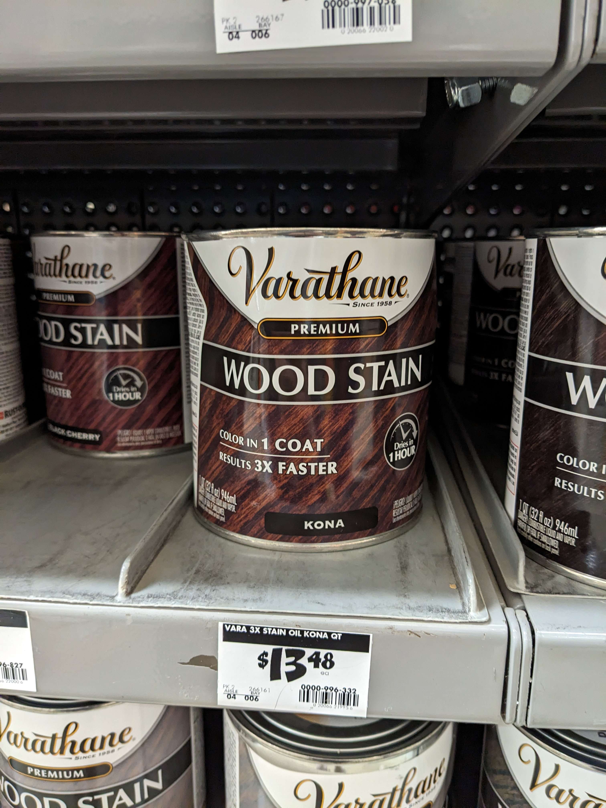
website/Team/progress/progress2pics/stain.jpg
