Avik127/RDNT/website/Team/progress/progress2pics/thursday_schem.png

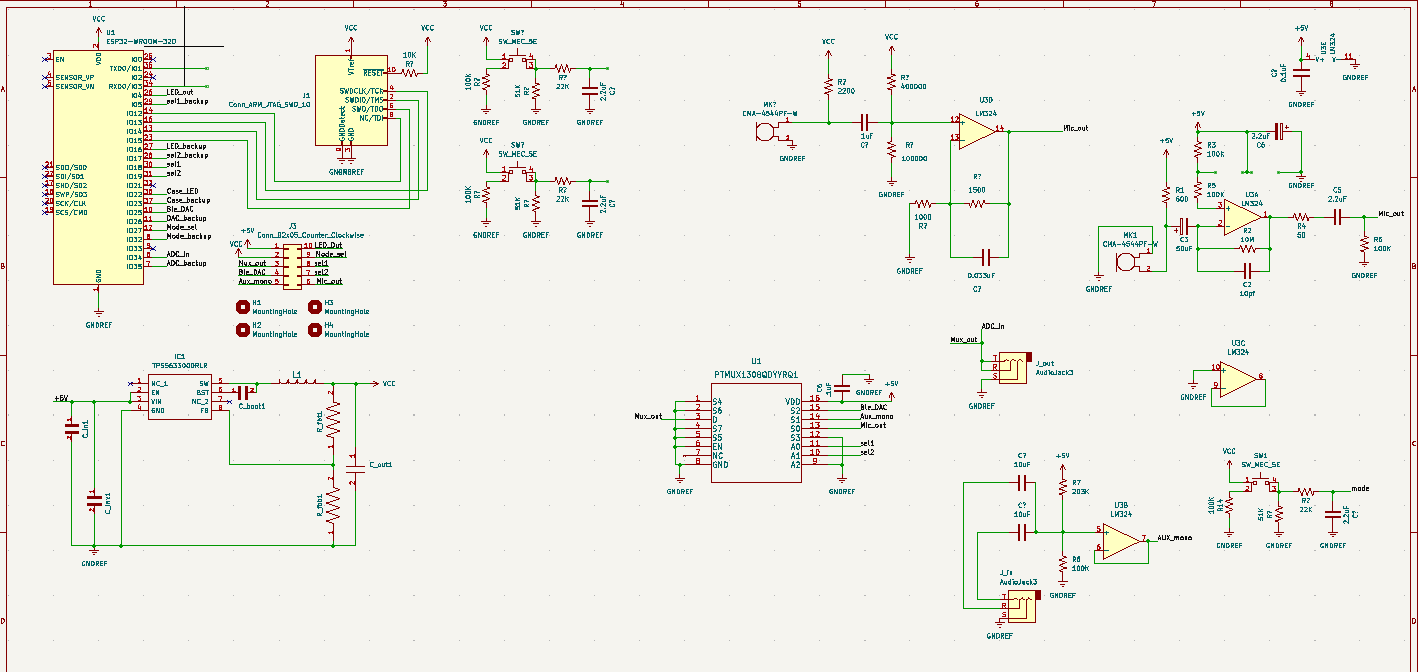
website/Team/progress/progress2pics/thursday_schem.png
