Avik127/RDNT/website/Team/progress/progress2pics/TMUX_circuit.jpg

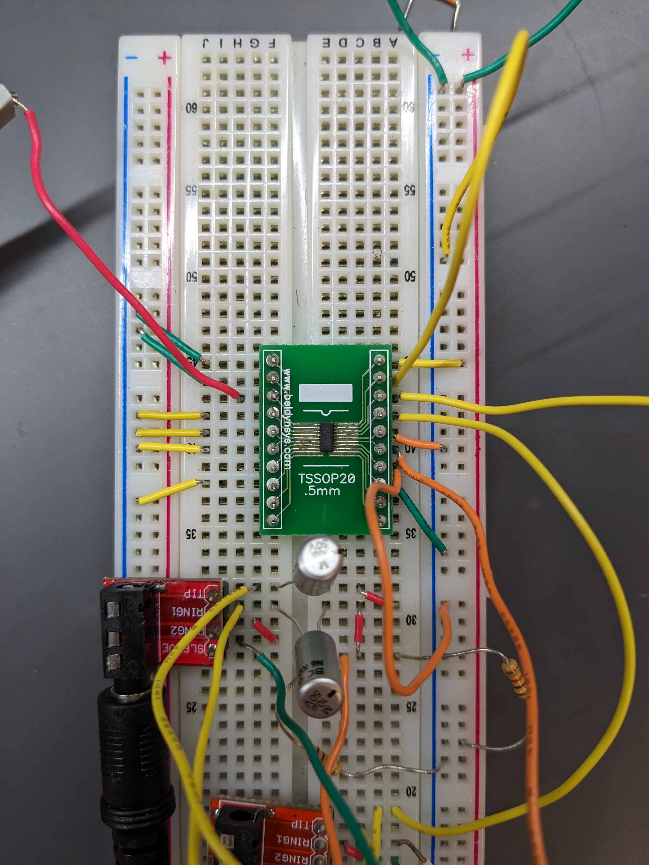
website/Team/progress/progress2pics/TMUX_circuit.jpg
