Avik127/RDNT/website/Team/progress/progress2pics/voltage_divider.jpg

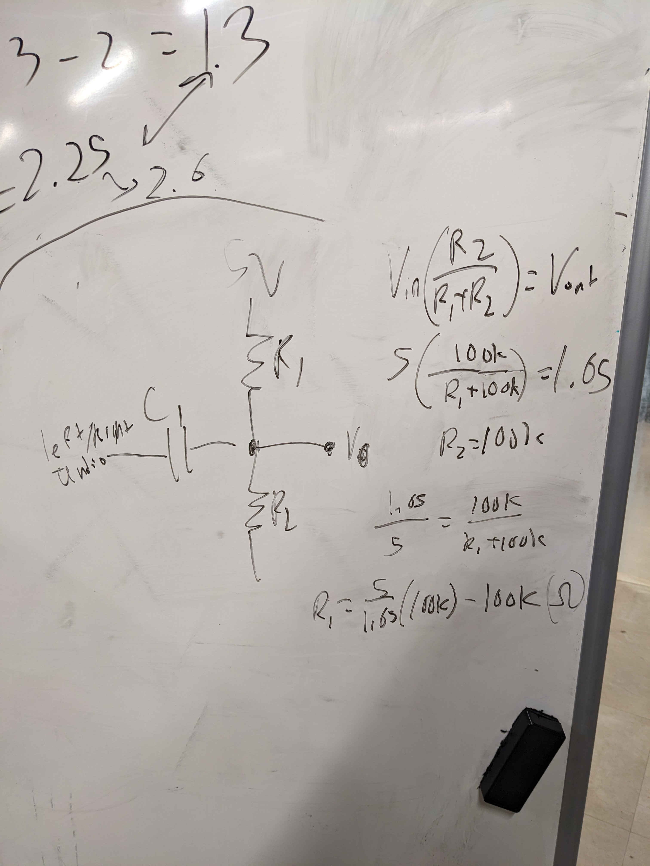
website/Team/progress/progress2pics/voltage_divider.jpg
