Avik127/RDNT/website/Team/progress/progress2pics/wave_to_ADC.jpg

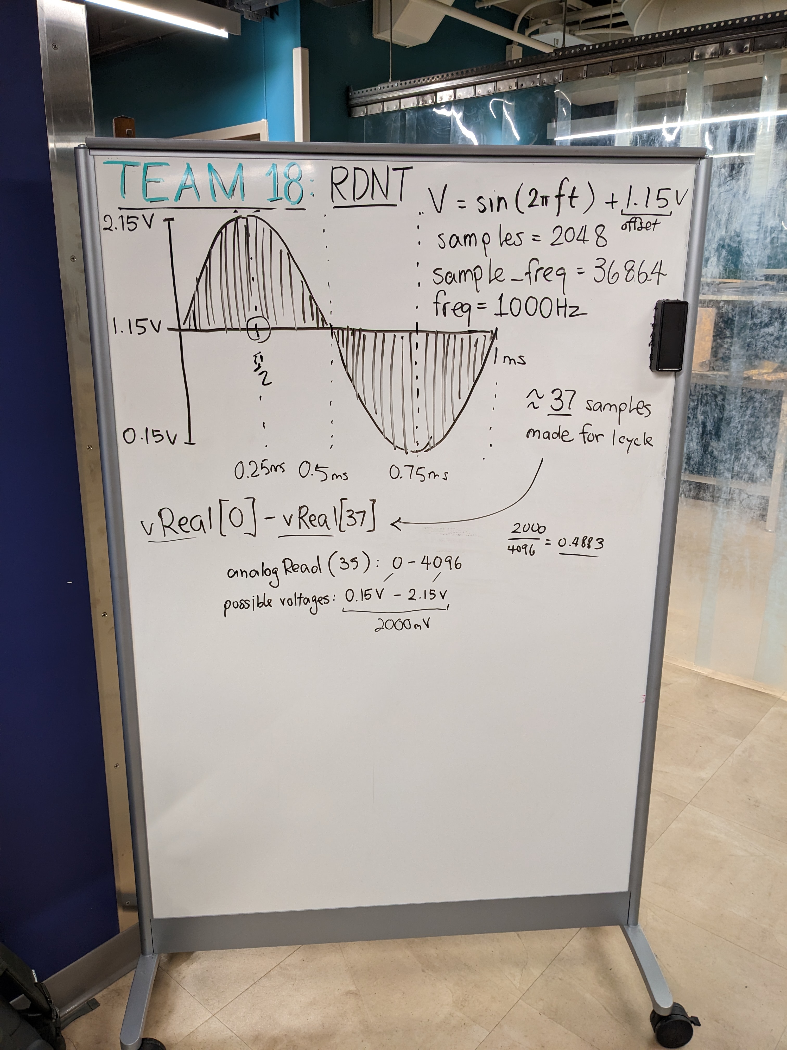
website/Team/progress/progress2pics/wave_to_ADC.jpg
