Avik127/RDNT/website/Team/progress/progress2pics/weird_freqs.png

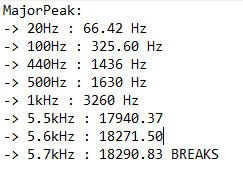
website/Team/progress/progress2pics/weird_freqs.png
