Avik127/RDNT/website/Team/progress/progress2pics/wood_1.jpg

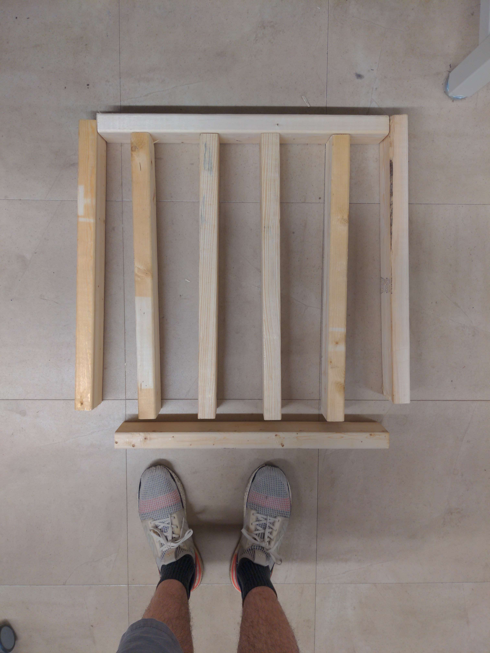
website/Team/progress/progress2pics/wood_1.jpg
