Avik127/RDNT/website/Team/progress/progress2pics/wood_2.jpg

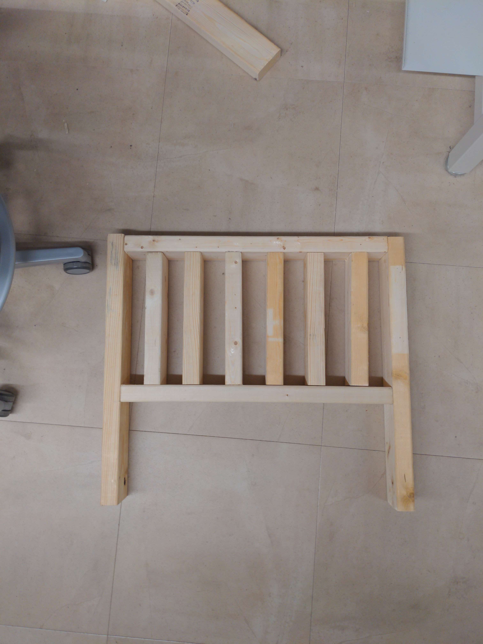
website/Team/progress/progress2pics/wood_2.jpg
