Avik127/RDNT/website/Team/progress/progress3pics.fld/image001.png

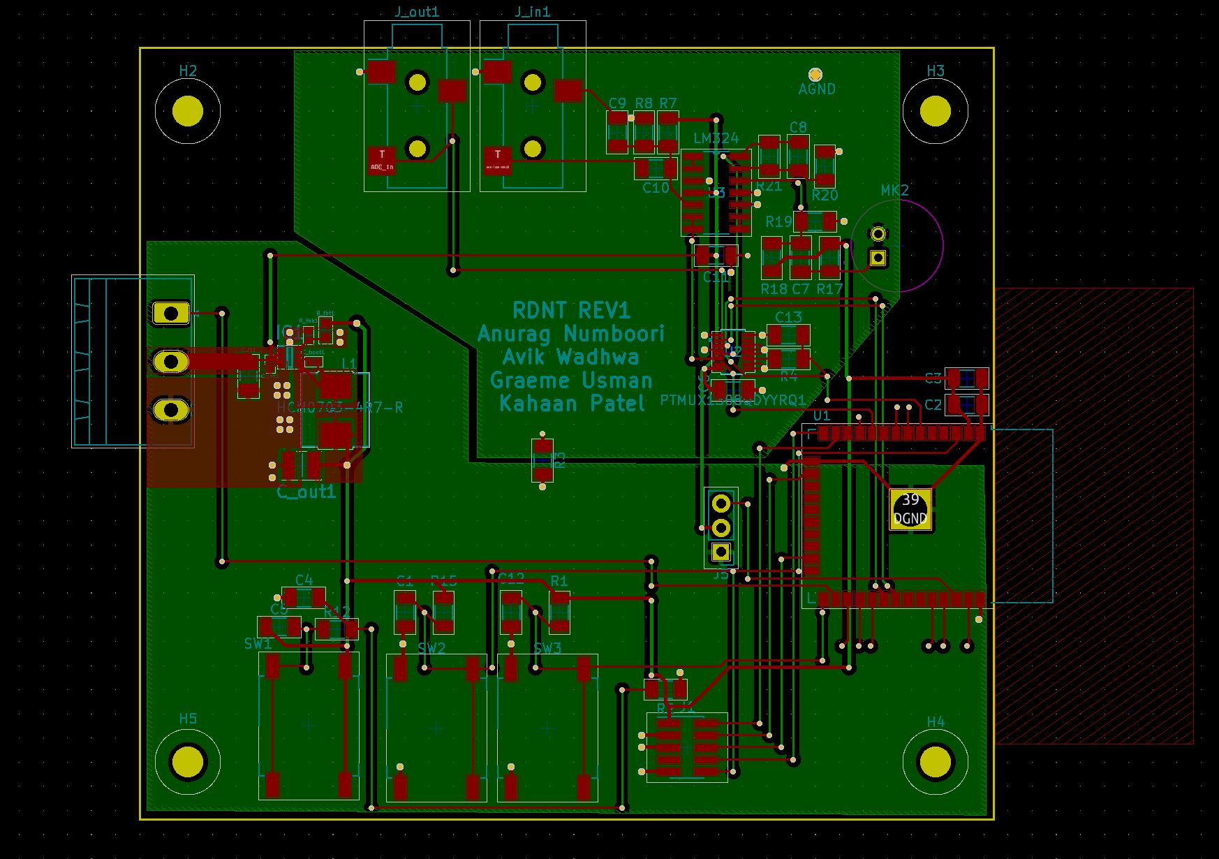
website/Team/progress/progress3pics.fld/image001.png
