Avik127/RDNT/website/Team/progress/progress3pics.fld/image003.png

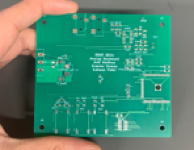
website/Team/progress/progress3pics.fld/image003.png
