Avik127/RDNT/website/Team/progress/progress3pics.fld/image004.png

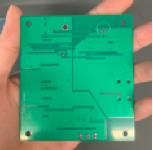
website/Team/progress/progress3pics.fld/image004.png
