Avik127/RDNT/website/Team/progress/progress3pics.fld/image005.png

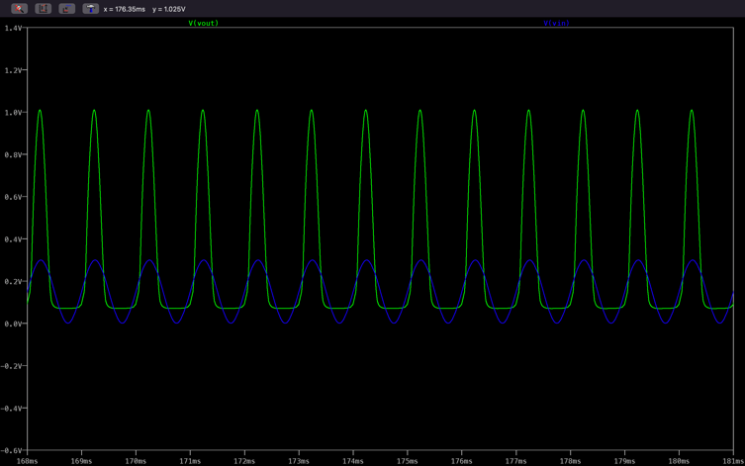
website/Team/progress/progress3pics.fld/image005.png
