Avik127/RDNT/website/Team/progress/progress3pics.fld/image006.png

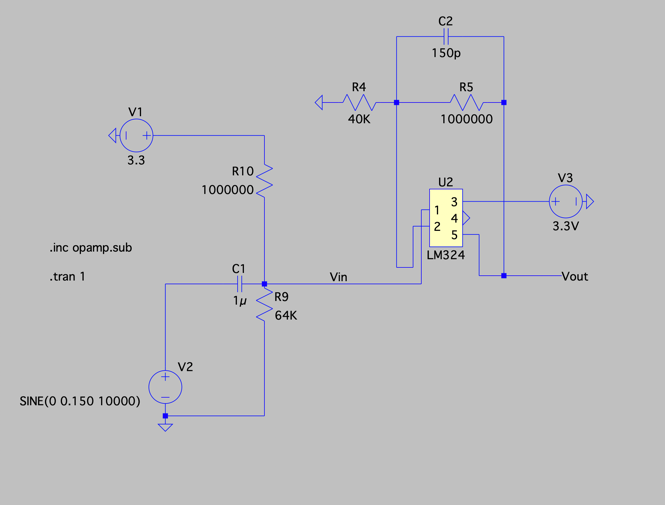
website/Team/progress/progress3pics.fld/image006.png
