Avik127/RDNT/website/Team/progress/progress3pics.fld/image007.png

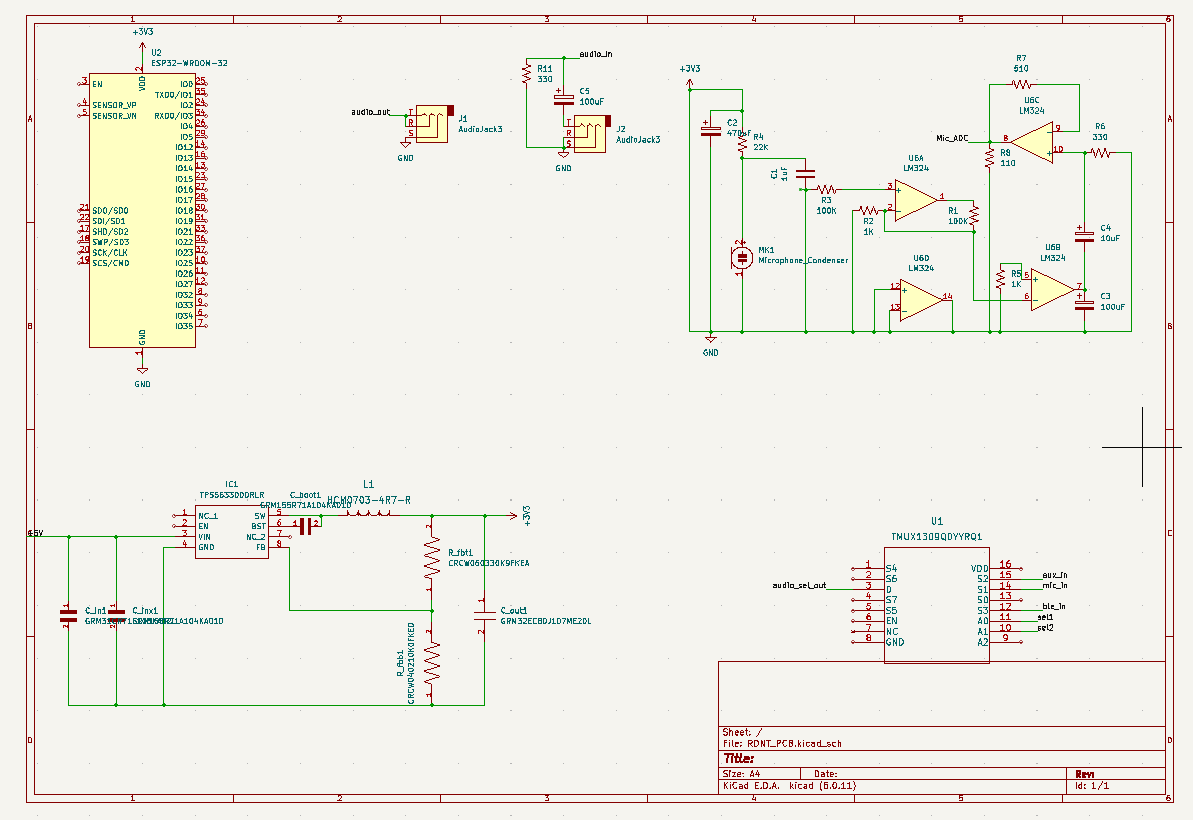
website/Team/progress/progress3pics.fld/image007.png
