Avik127/RDNT/website/Team/progress/progress3pics.fld/image008.png

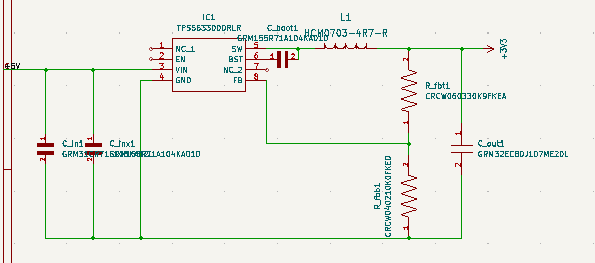
website/Team/progress/progress3pics.fld/image008.png
