Avik127/RDNT/website/Team/progress/progress3pics.fld/image010.png

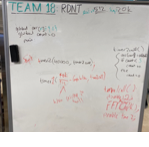
website/Team/progress/progress3pics.fld/image010.png
