Avik127/RDNT/website/Team/progress/progress3pics.fld/image011.png

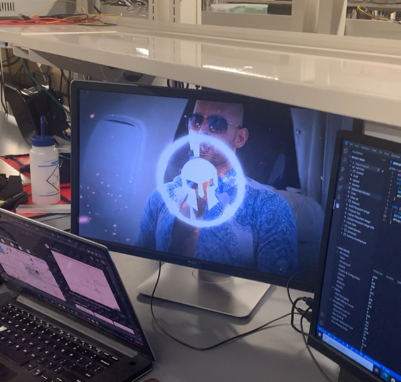
website/Team/progress/progress3pics.fld/image011.png
