Avik127/RDNT/website/Team/progress/progress3pics.fld/image012.png

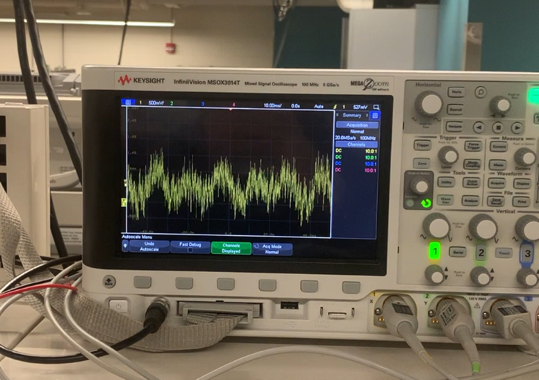
website/Team/progress/progress3pics.fld/image012.png
