Avik127/RDNT/website/Team/progress/progress3pics.fld/image015.png

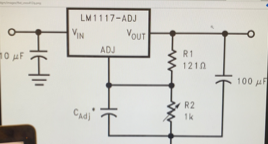
website/Team/progress/progress3pics.fld/image015.png
