Avik127/RDNT/website/Team/progress/progress3pics/image001.jpg

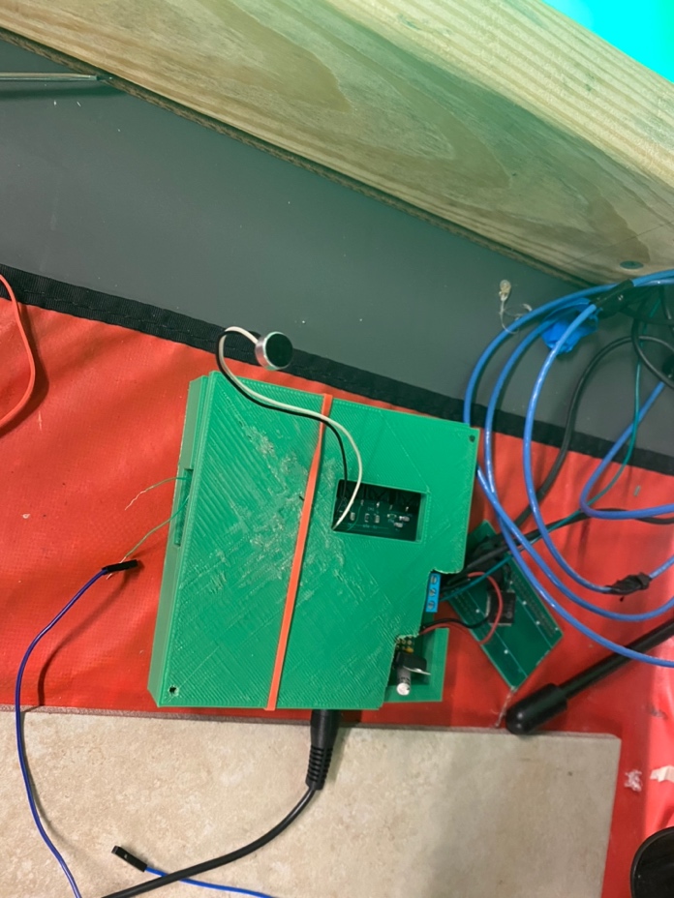
website/Team/progress/progress3pics/image001.jpg
