Avik127/RDNT/website/Team/progress/progress3pics/image002.png

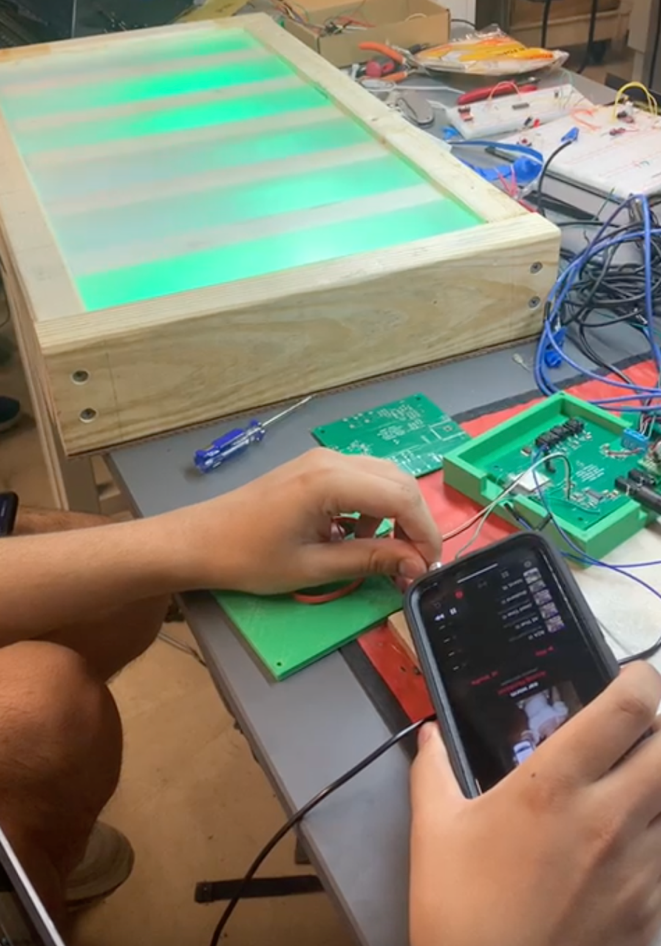
website/Team/progress/progress3pics/image002.png
