Avik127/RDNT/website/Team/progress/progress3pics/image003.jpg

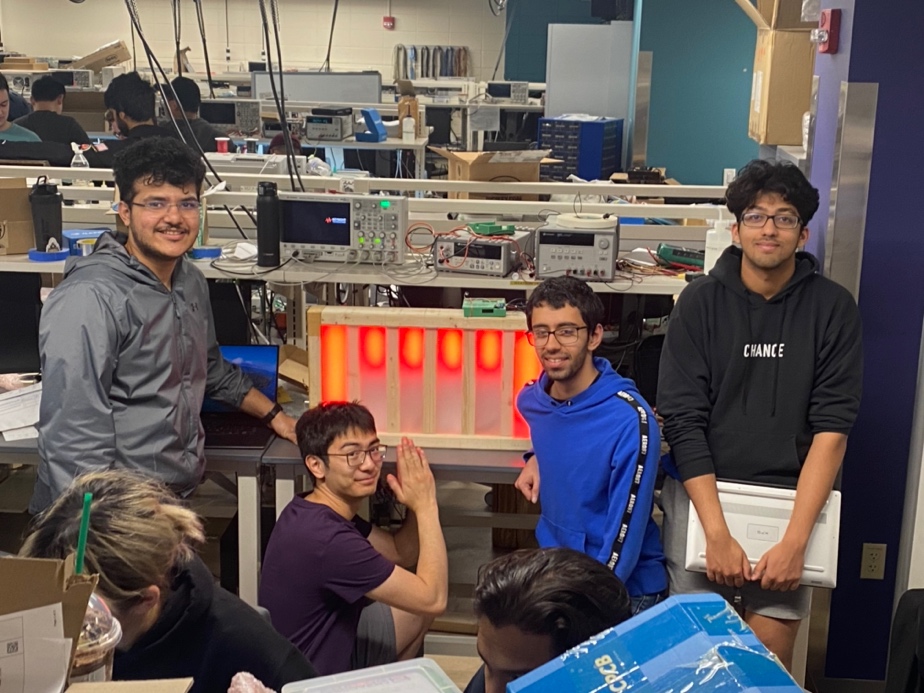
website/Team/progress/progress3pics/image003.jpg
