Avik127/RDNT/website/Team/progress/progress3pics/image004.jpg

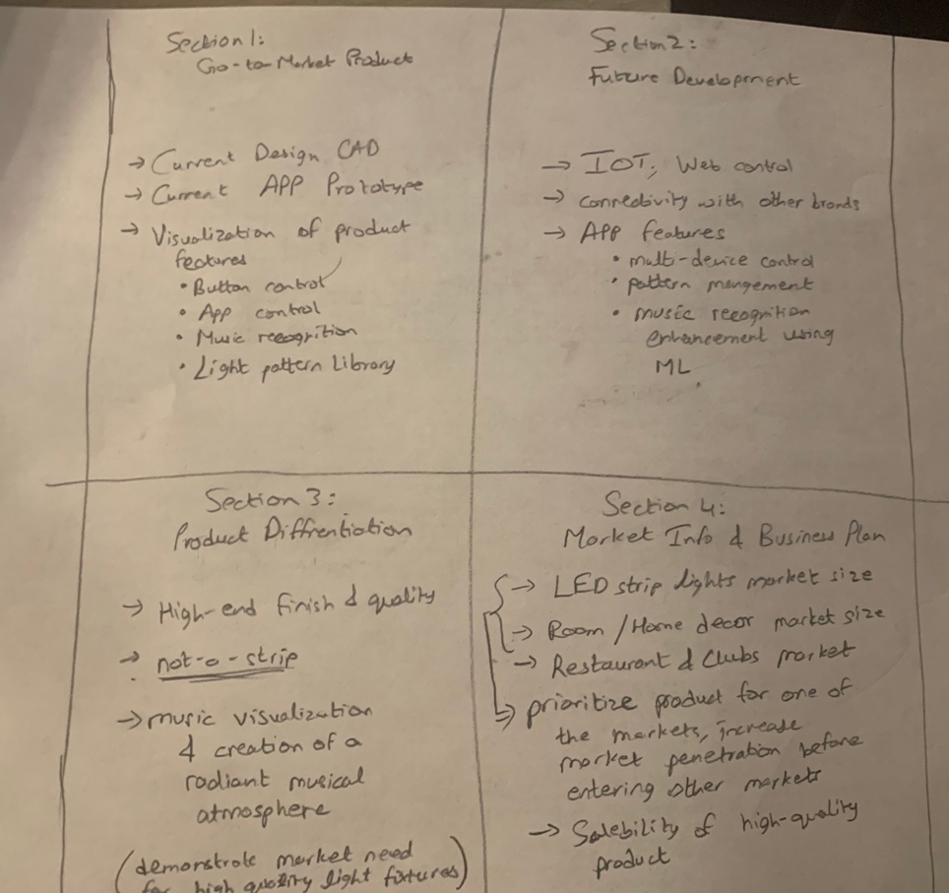
website/Team/progress/progress3pics/image004.jpg
