Avik127/RDNT/website/Team/progress/progress3pics/image005.jpg

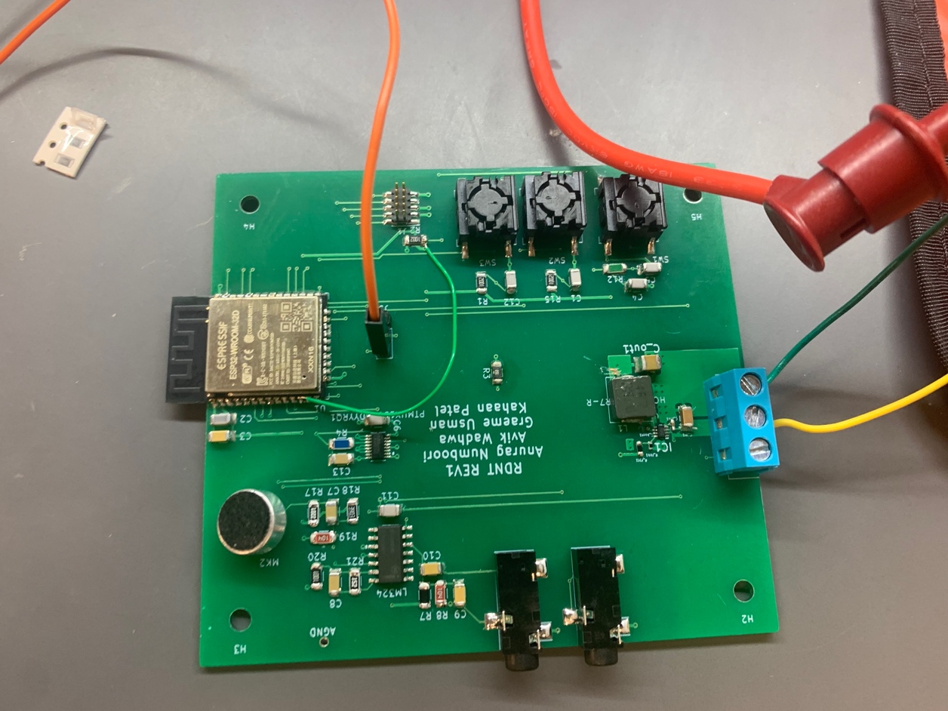
website/Team/progress/progress3pics/image005.jpg
