Avik127/RDNT/website/Team/progress/progress3pics/image006.jpg

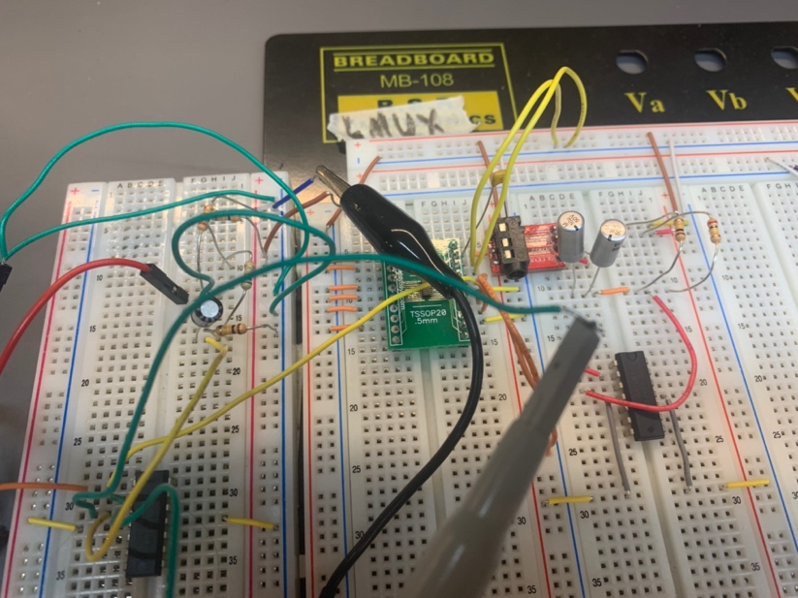
website/Team/progress/progress3pics/image006.jpg
