Avik127/RDNT/website/Team/progress/progress3pics/image008.jpg

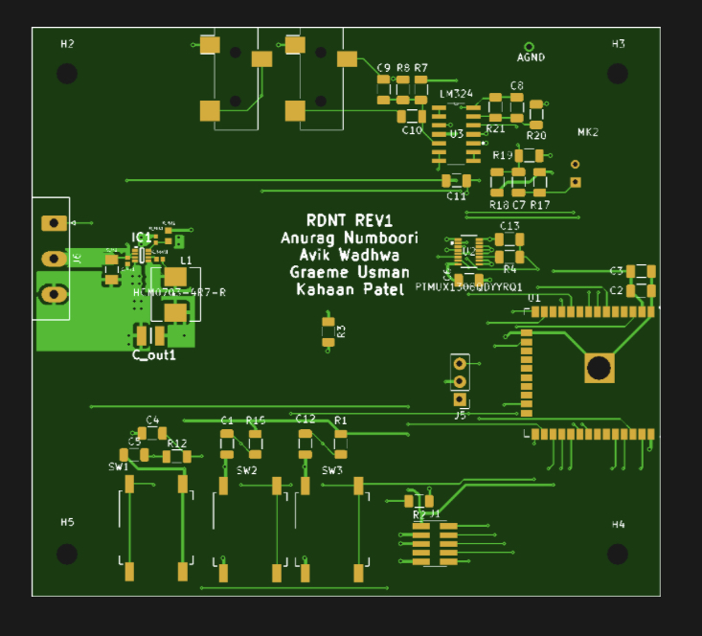
website/Team/progress/progress3pics/image008.jpg
