Avik127/RDNT/website/Team/progress/progress3pics/image017.jpg

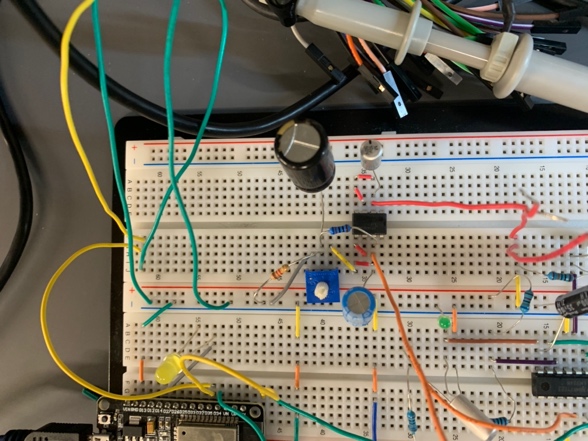
website/Team/progress/progress3pics/image017.jpg
