Avik127/RDNT/website/Team/progress/progress3pics/image019.jpg

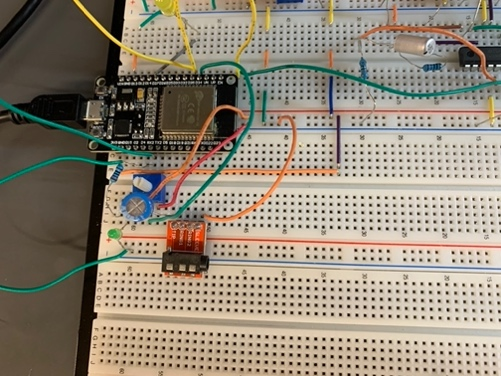
website/Team/progress/progress3pics/image019.jpg
