Avik127/RDNT/website/Team/progress/progress3pics/image022.png

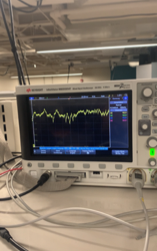
website/Team/progress/progress3pics/image022.png
