Avik127/RDNT/website/Team/progress/progress3pics/image023.png

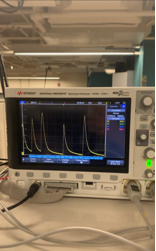
website/Team/progress/progress3pics/image023.png
