Avik127/RDNT/website/Team/progress/progress3pics/image024.png

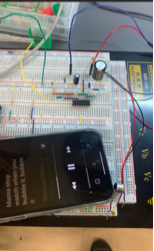
website/Team/progress/progress3pics/image024.png
