Avik127/RDNT/website/Team/progress/progress3pics/image026.jpg

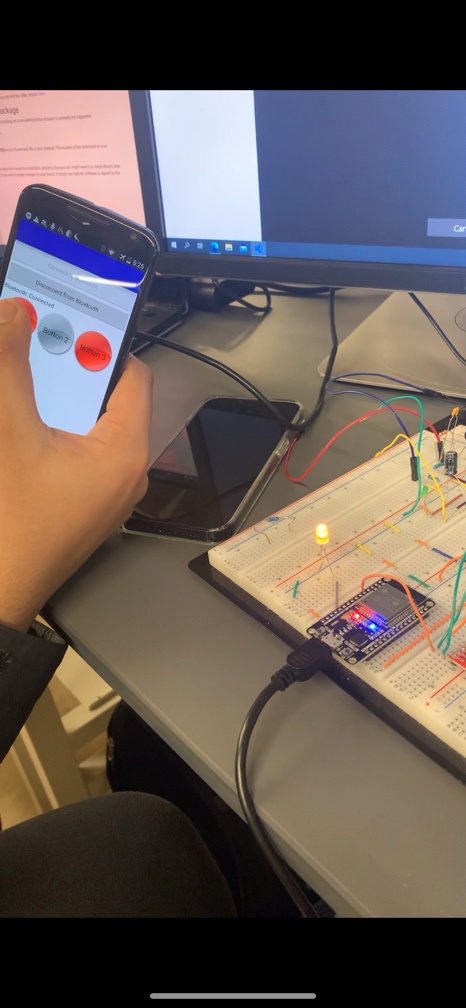
website/Team/progress/progress3pics/image026.jpg
