Avik127/RDNT/website/Team/progress/resources4/androidApp.png

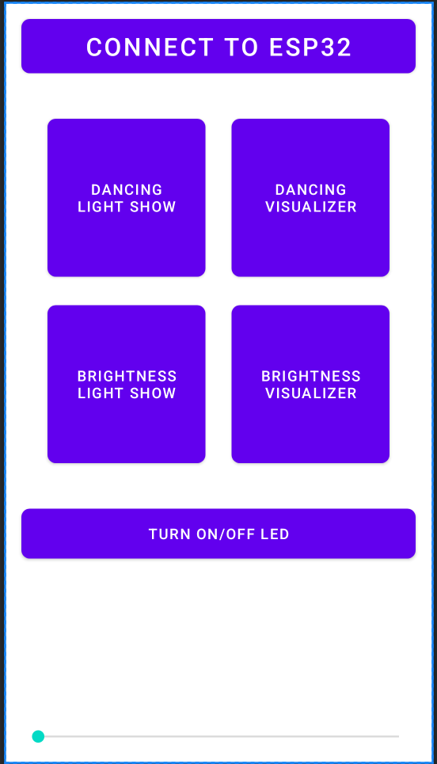
website/Team/progress/resources4/androidApp.png
