Avik127/RDNT/website/Team/progress/resources4/androidnewApp.png

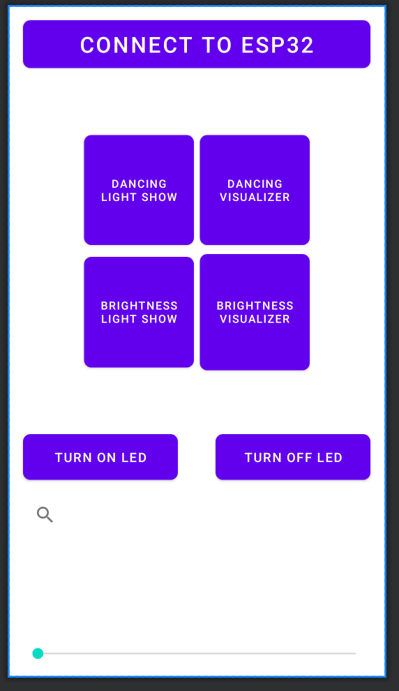
website/Team/progress/resources4/androidnewApp.png
