Avik127/RDNT/website/Team/progress/resources4/app.png

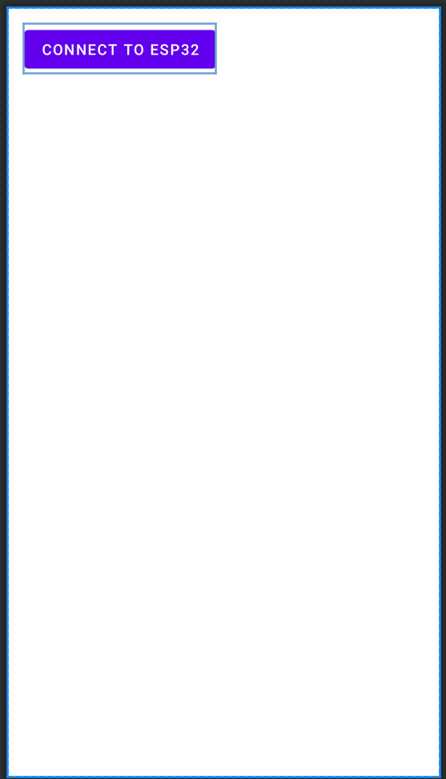
website/Team/progress/resources4/app.png
