Avik127/RDNT/website/Team/progress/resources4/codeLogic.jpeg

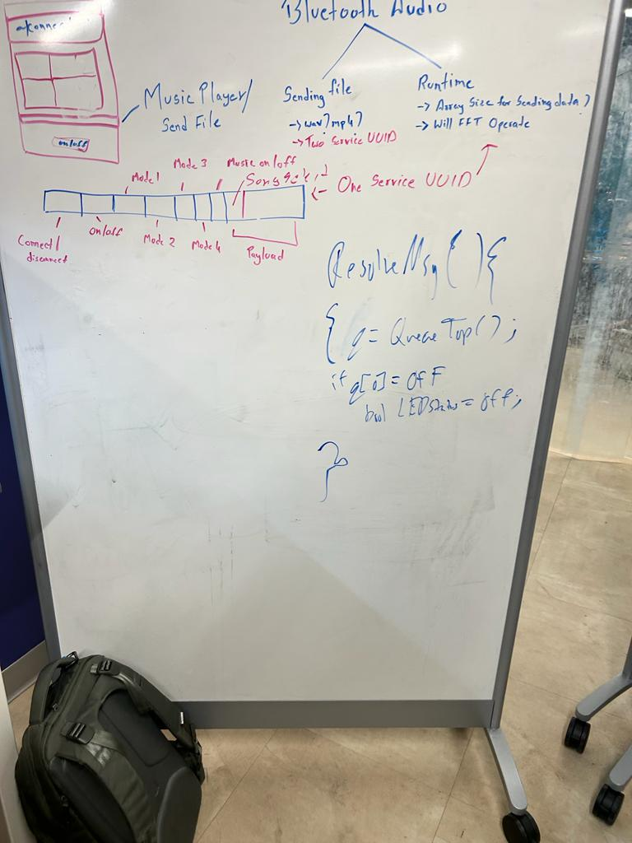
website/Team/progress/resources4/codeLogic.jpeg
