Avik127/RDNT/website/Team/progress/resources4/design01.jpeg

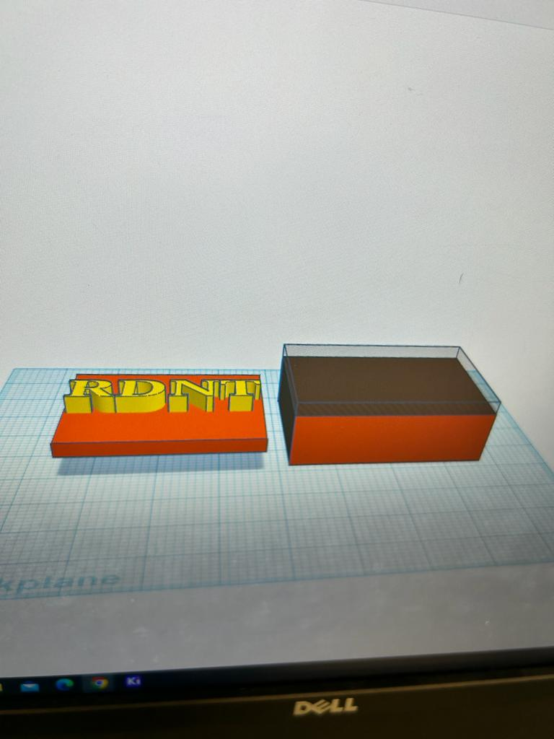
website/Team/progress/resources4/design01.jpeg
