Avik127/RDNT/website/Team/progress/resources4/InvertingLM324.png

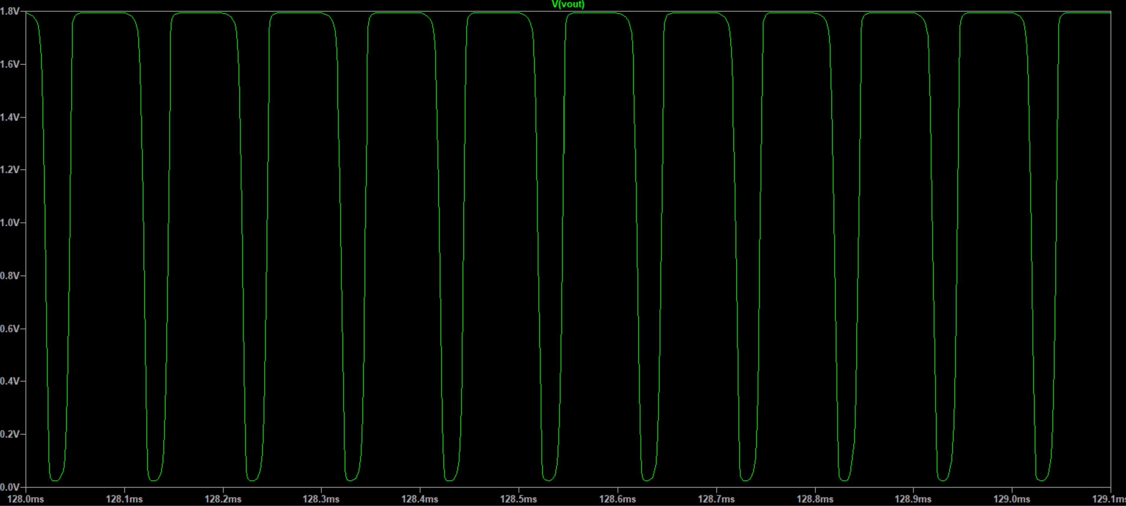
website/Team/progress/resources4/InvertingLM324.png
