Avik127/RDNT/website/Team/progress/resources4/LTspiceLM117.png

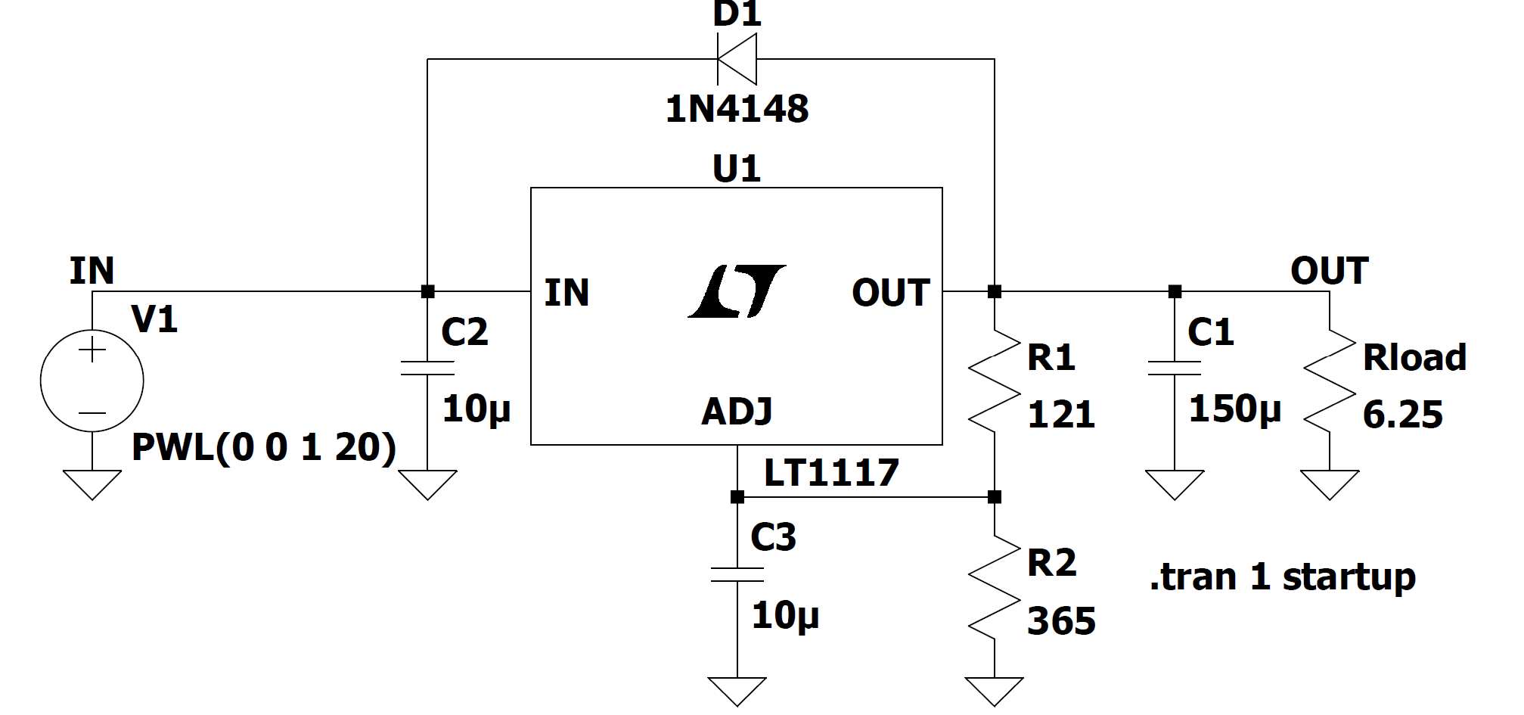
website/Team/progress/resources4/LTspiceLM117.png
