Avik127/RDNT/website/Team/progress/resources4/profile.jpeg

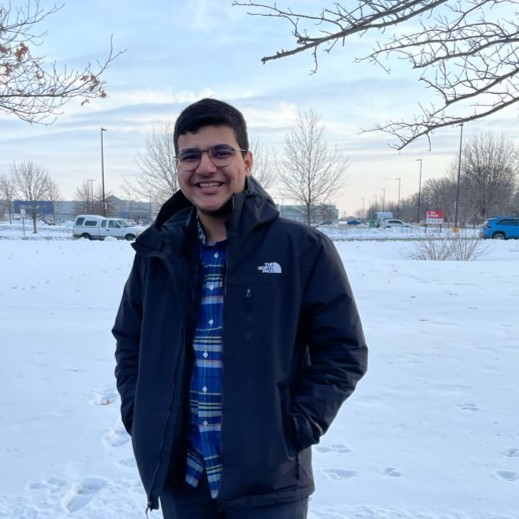
website/Team/progress/resources4/profile.jpeg
