Avik127/RDNT/website/Team/progress/resources4/RDNT - DC_DC Regulator.jpg

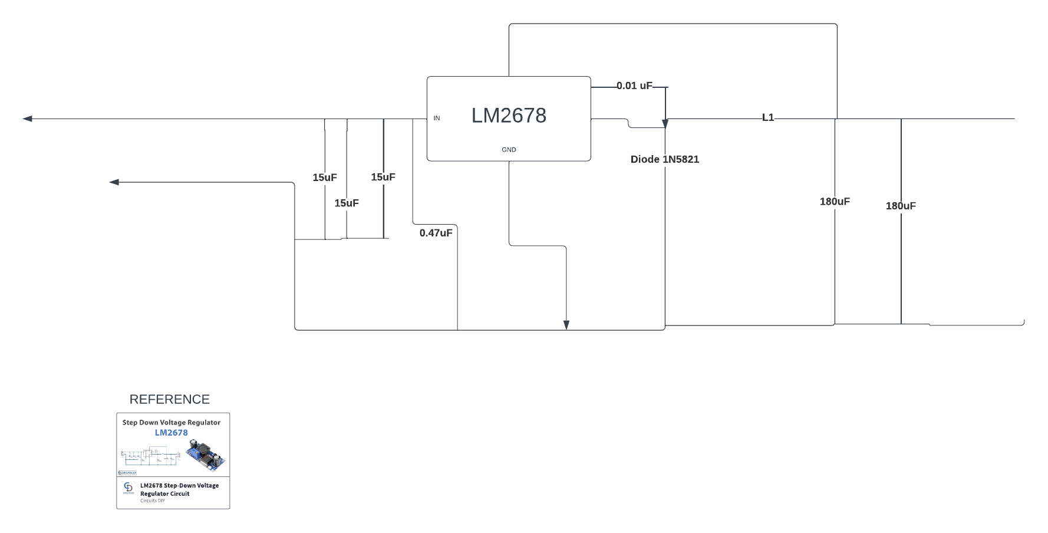
website/Team/progress/resources4/RDNT - DC_DC Regulator.jpg
