Avik127/RDNT/website/Team/progress/resources4/RDNT - Full Diagram.jpg

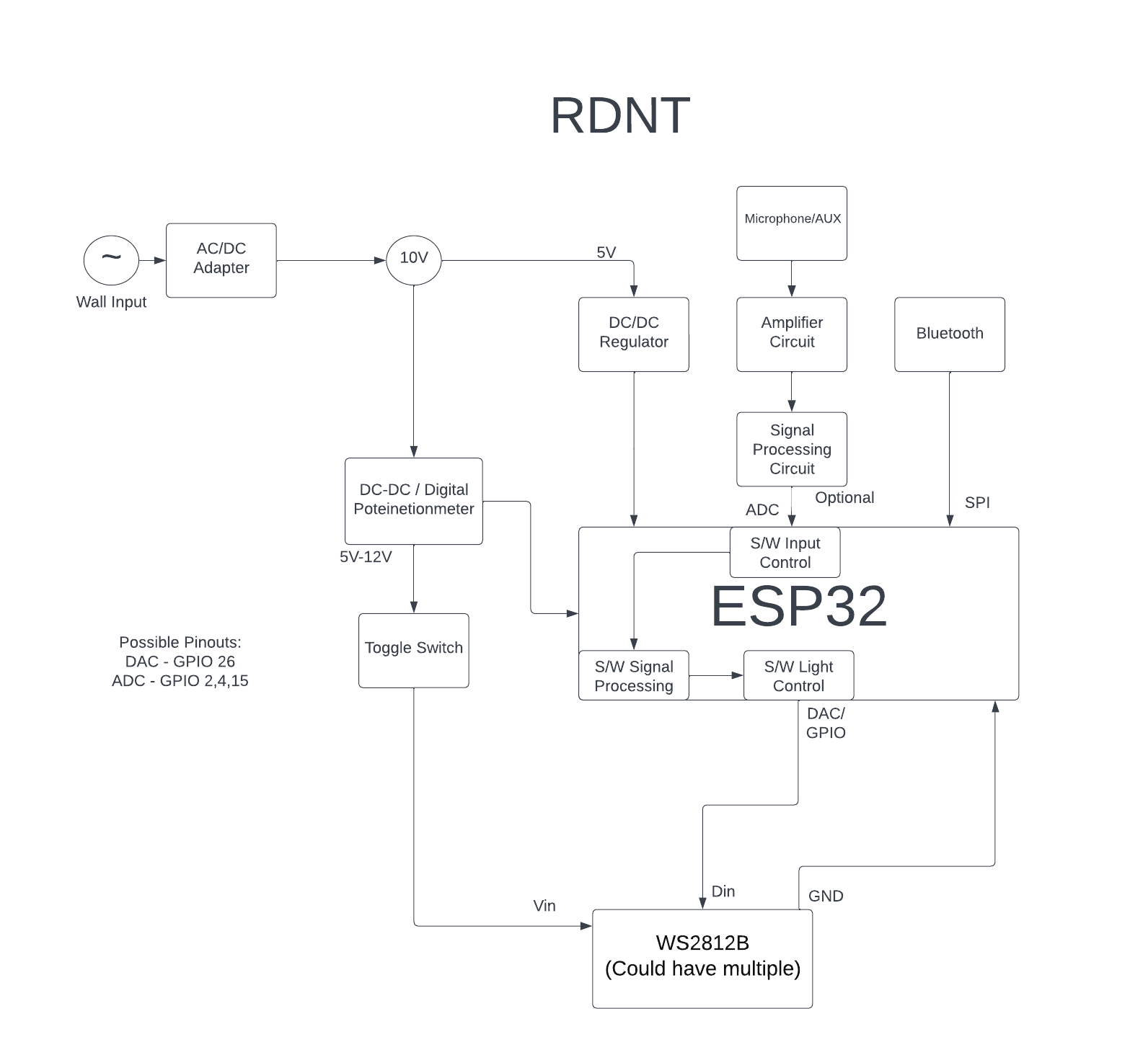
website/Team/progress/resources4/RDNT - Full Diagram.jpg
