Avik127/RDNT/website/Team/progress/resources4/SimulationLM324.png

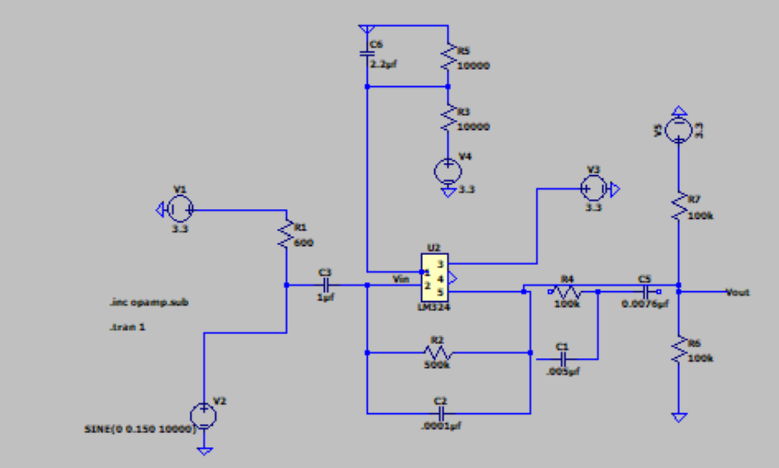
website/Team/progress/resources4/SimulationLM324.png
