Avik127/RDNT/website/Team/progress/progress2pics/final_construction.jpg

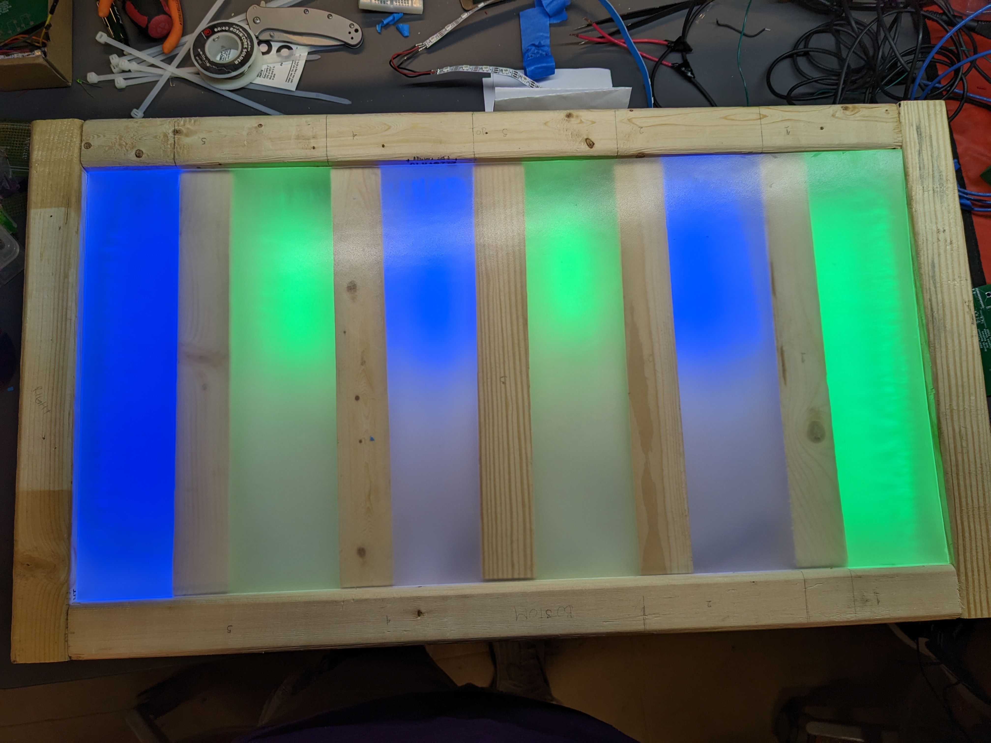
website/Team/progress/progress2pics/final_construction.jpg
