Avik127/RDNT/website/Team/progress/progress2pics/microphone_soldered.jpg

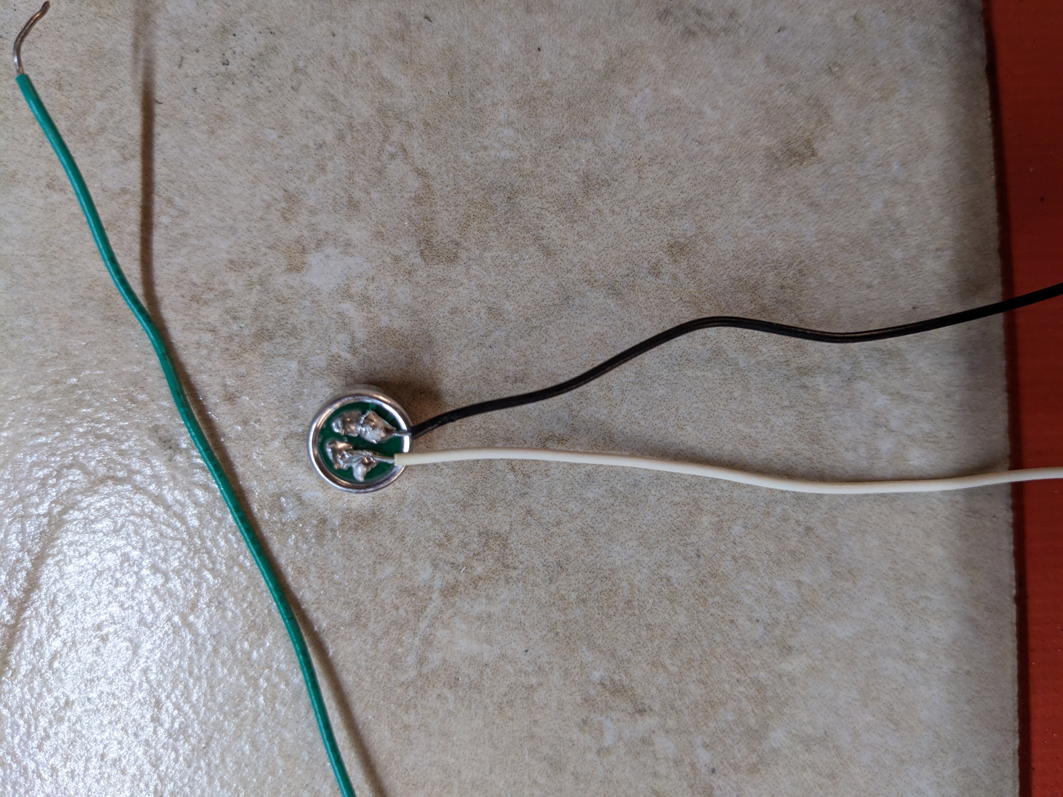
website/Team/progress/progress2pics/microphone_soldered.jpg
