Avik127/RDNT/website/Team/progress/progress2pics/PCB_code_testing.jpg

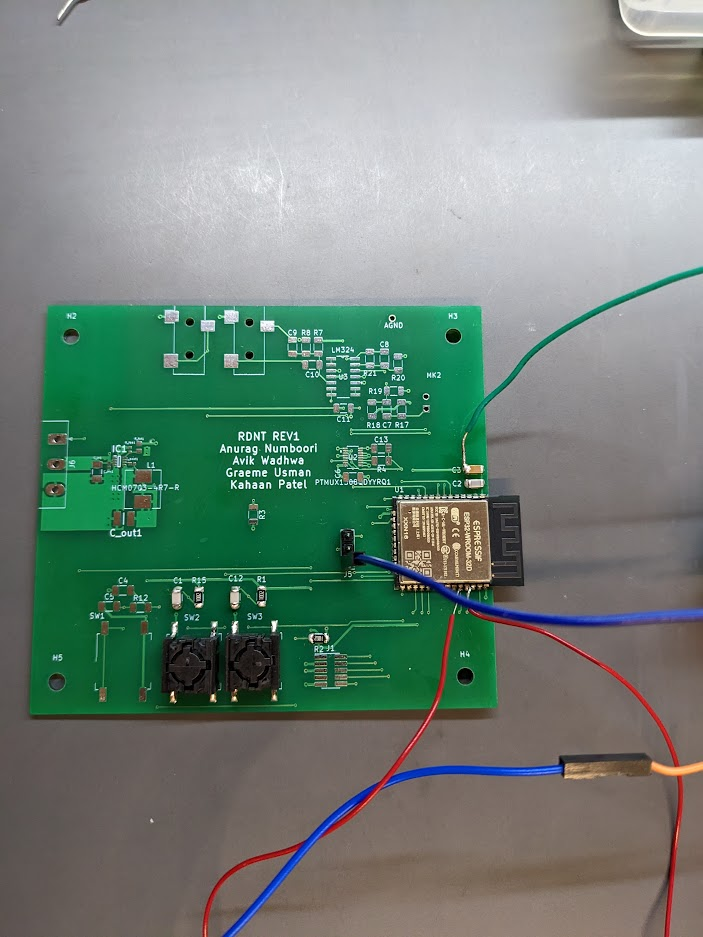
website/Team/progress/progress2pics/PCB_code_testing.jpg
