Avik127/RDNT/website/Team/progress/progress2pics/PCB_separate_power_test.jpg

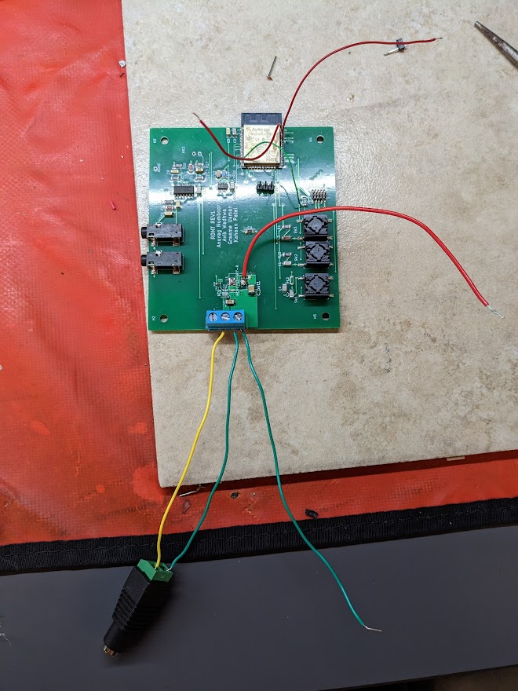
website/Team/progress/progress2pics/PCB_separate_power_test.jpg
