Avik127/RDNT/website/Team/progress/progress2pics/testing_analog_signals.jpg

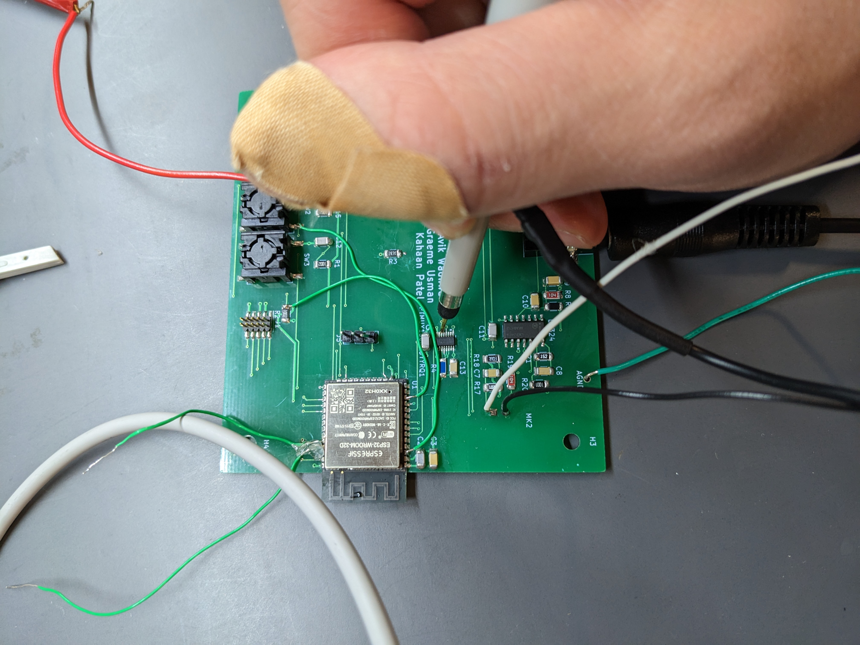
website/Team/progress/progress2pics/testing_analog_signals.jpg
