Avik127/RDNT/RDNT_Firmware/Prototyping Tools/ESP_PCB_FFT_ACinput.c

#include <stdio.h>
#include <stdlib.h>
#include <string.h>
#include "freertos/FreeRTOS.h"
#include "freertos/task.h"
#include "esp_system.h"
#include "driver/spi_master.h"
#include "soc/gpio_struct.h"
#include "driver/gpio.h"
#include "driver/uart.h"
#include "soc/uart_struct.h"
#include <math.h>

#include "esp_dsp.h"

static const char *TAG = "main";

// This example shows how to use FFT from esp-dsp library

#define N_SAMPLES 256
int N = N_SAMPLES;
// Input test array
__attribute__((aligned(16))) float x1[N_SAMPLES] = {1.826514,
                                                    1.825610,
                                                    1.792188,
                                                    1.794897,
                                                    1.763515,
                                                    1.739594,
                                                    1.711385,
                                                    1.683736,
                                                    1.659273,
                                                    1.638171,
                                                    1.621557,
                                                    1.609940,
                                                    1.600132,
                                                    1.591181,
                                                    1.584774,
                                                    1.579577,
                                                    1.570907,
                                                    1.556519,
                                                    1.540313,
                                                    1.528084,
                                                    1.520652,
                                                    1.514693,
                                                    1.504429,
                                                    1.486382,
                                                    1.463650,
                                                    1.439511,
                                                    1.414848,
                                                    1.391892,
                                                    1.371594,
                                                    1.353437,
                                                    1.332913,
                                                    1.304003,
                                                    1.270026,
                                                    1.238130,
                                                    1.206437,
                                                    1.174754,
                                                    1.146739,
                                                    1.124371,
                                                    1.109086,
                                                    1.101391,
                                                    1.101799,
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
// Window coefficients
__attribute__((aligned(16))) float wind[N_SAMPLES];
// working complex array
__attribute__((aligned(16))) float y_cf[N_SAMPLES * 2];
// Pointers to result arrays
float *y1_cf = &y_cf[0];

// Sum of y1 and y2
__attribute__((aligned(16))) float sum_y[N_SAMPLES / 2];

void app_main()
{
    esp_err_t ret;
    ESP_LOGI(TAG, "Start Example.");
    ret = dsps_fft2r_init_fc32(NULL, CONFIG_DSP_MAX_FFT_SIZE);
    if (ret != ESP_OK)
    {
        ESP_LOGE(TAG, "Not possible to initialize FFT. Error = %i", ret);
        return;
    }

    // Generate hann window
    dsps_wind_hann_f32(wind, N);
    
    // for (int i = 0; i < N; i++)
    // {
    //     printf("%f\n", x1[i]);
    // }

    // Convert two input vectors to one complex vector
    for (int i = 0; i < N; i++)
    {
        y_cf[i * 2 + 0] = x1[i] * wind[i];
        y_cf[i * 2 + 1] = 0 * wind[i];
    }
    // FFT
    unsigned int start_b = dsp_get_cpu_cycle_count();
    dsps_fft2r_fc32(y_cf, N);
    unsigned int end_b = dsp_get_cpu_cycle_count();
    // Bit reverse
    dsps_bit_rev_fc32(y_cf, N);
    // Convert one complex vector to two complex vectors
    dsps_cplx2reC_fc32(y_cf, N);

    for (int i = 0; i < N / 2; i++)
    {
        y1_cf[i] = 10 * log10f((y1_cf[i * 2 + 0] * y1_cf[i * 2 + 0] + y1_cf[i * 2 + 1] * y1_cf[i * 2 + 1]) / N);
    }

    for (int i = 0; i < N / 2; i++)
    {
        printf("%f\n", y1_cf[i]);
    }

    // Show power spectrum in 64x10 window from -100 to 0 dB from 0..N/4 samples
    ESP_LOGW(TAG, "Signal x1");
    dsps_view(y1_cf, N / 2, 64, 10, -60, 40, '|');
    // ESP_LOGW(TAG, "Signal x2");
    // dsps_view(y2_cf, N / 2, 64, 10, -60, 40, '|');
    // ESP_LOGW(TAG, "Signals x1 and x2 on one plot");
    // dsps_view(sum_y, N / 2, 64, 10, -60, 40, '|');
    ESP_LOGI(TAG, "FFT for %i complex points take %i cycles", N, end_b - start_b);

    ESP_LOGI(TAG, "End Example.");
}
