Avik127/RDNT/website/Team/progress/progress1pics/anu.jpg

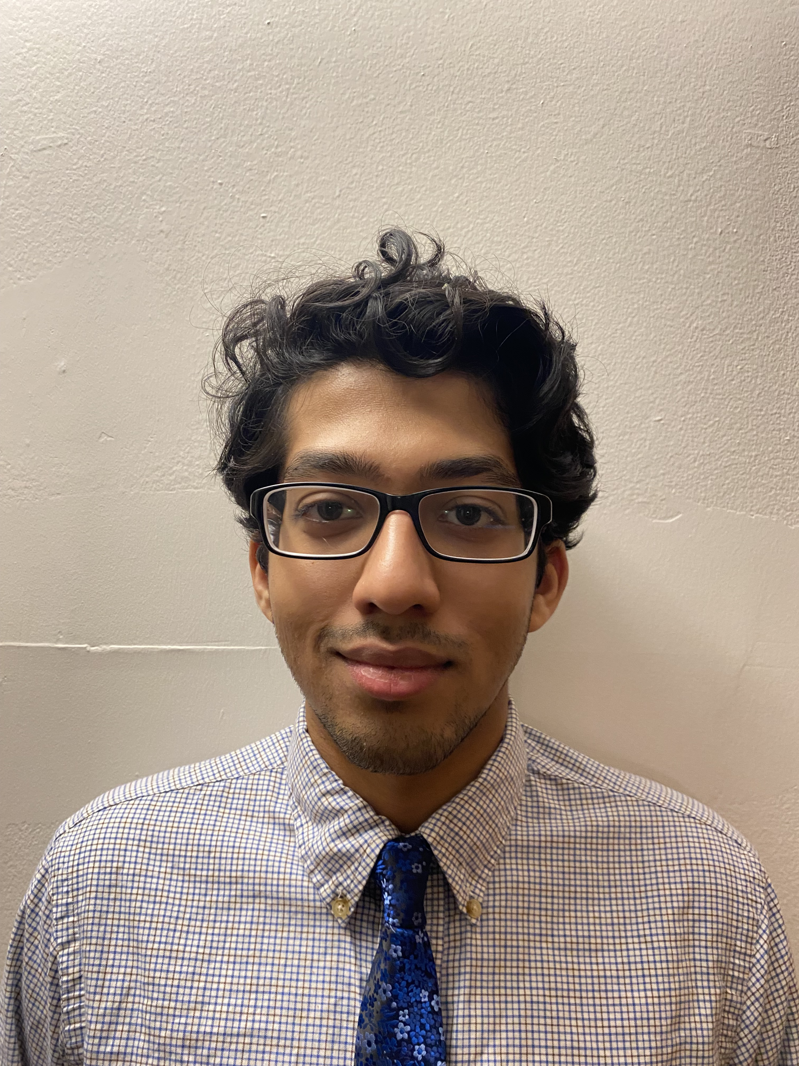
website/Team/progress/progress1pics/anu.jpg
