Avik127/RDNT/website/Team/progress/progress1pics/formulas.jpg

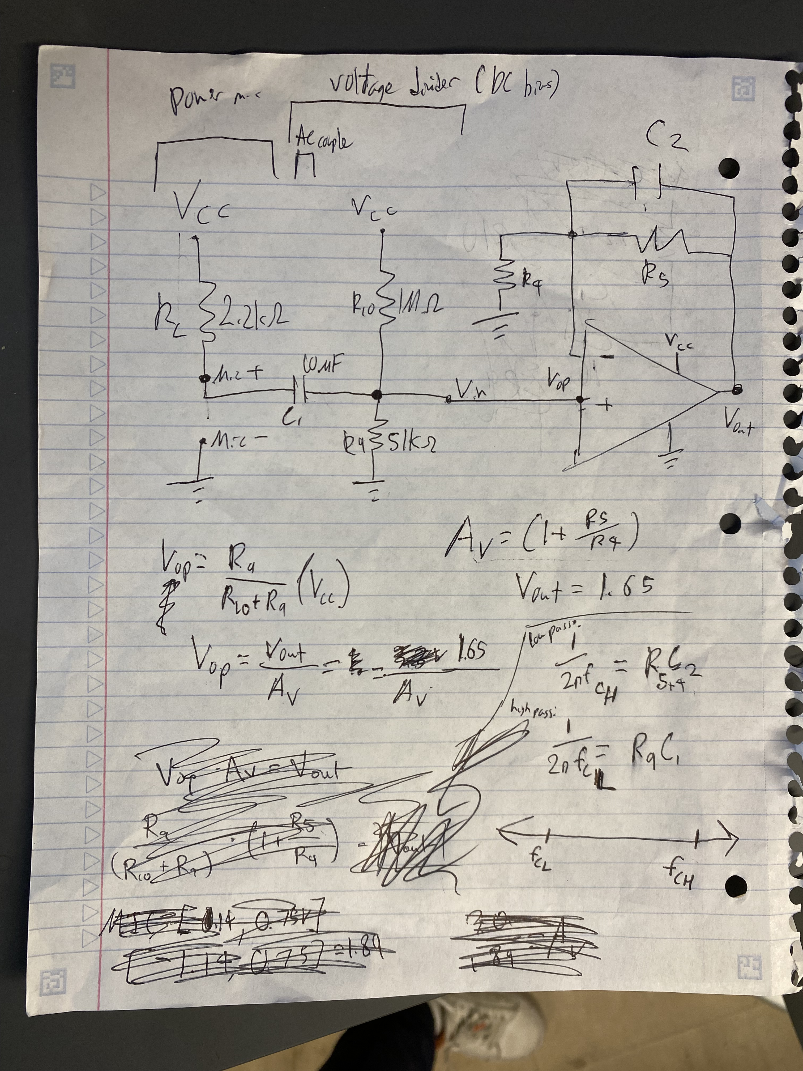
website/Team/progress/progress1pics/formulas.jpg
