Avik127/RDNT/website/Team/progress/progress1pics/plank.jpg

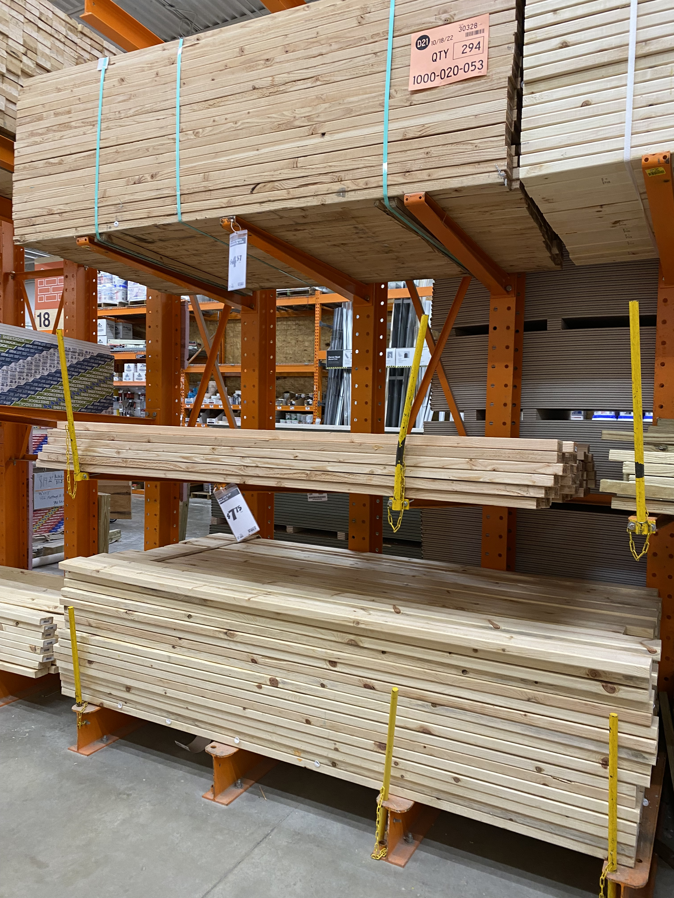
website/Team/progress/progress1pics/plank.jpg
