Avik127/RDNT/website/Team/progress/progress2pics/aux_in_out.jpg

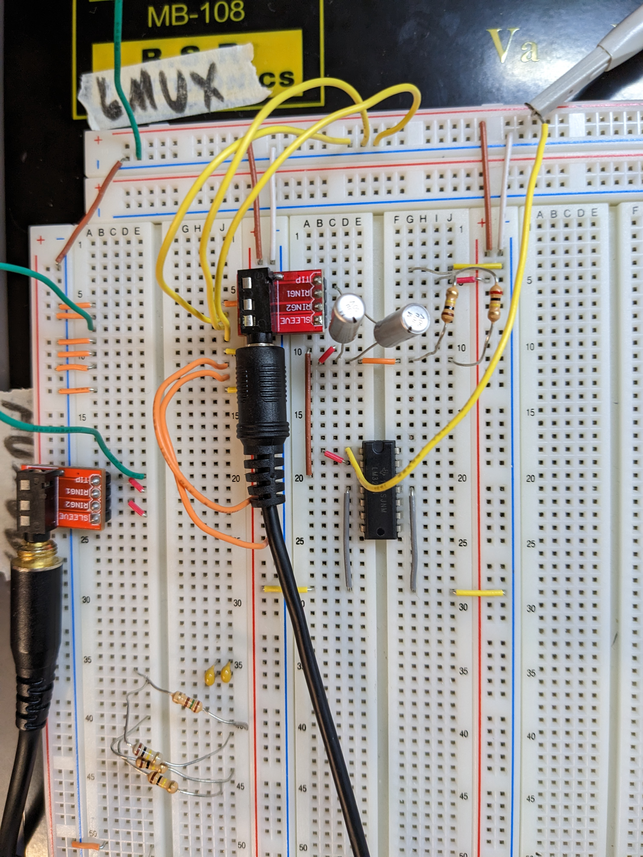
website/Team/progress/progress2pics/aux_in_out.jpg
