Avik127/RDNT/website/Team/progress/progress2pics/aux_into_mux.jpg

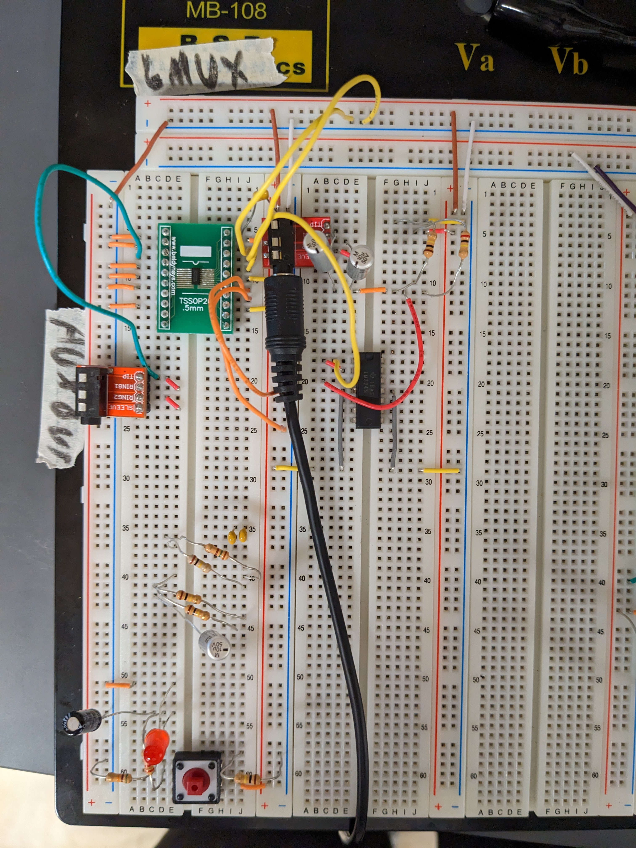
website/Team/progress/progress2pics/aux_into_mux.jpg
