Avik127/RDNT/website/Team/progress/progress2pics/mic_circuit.jpg

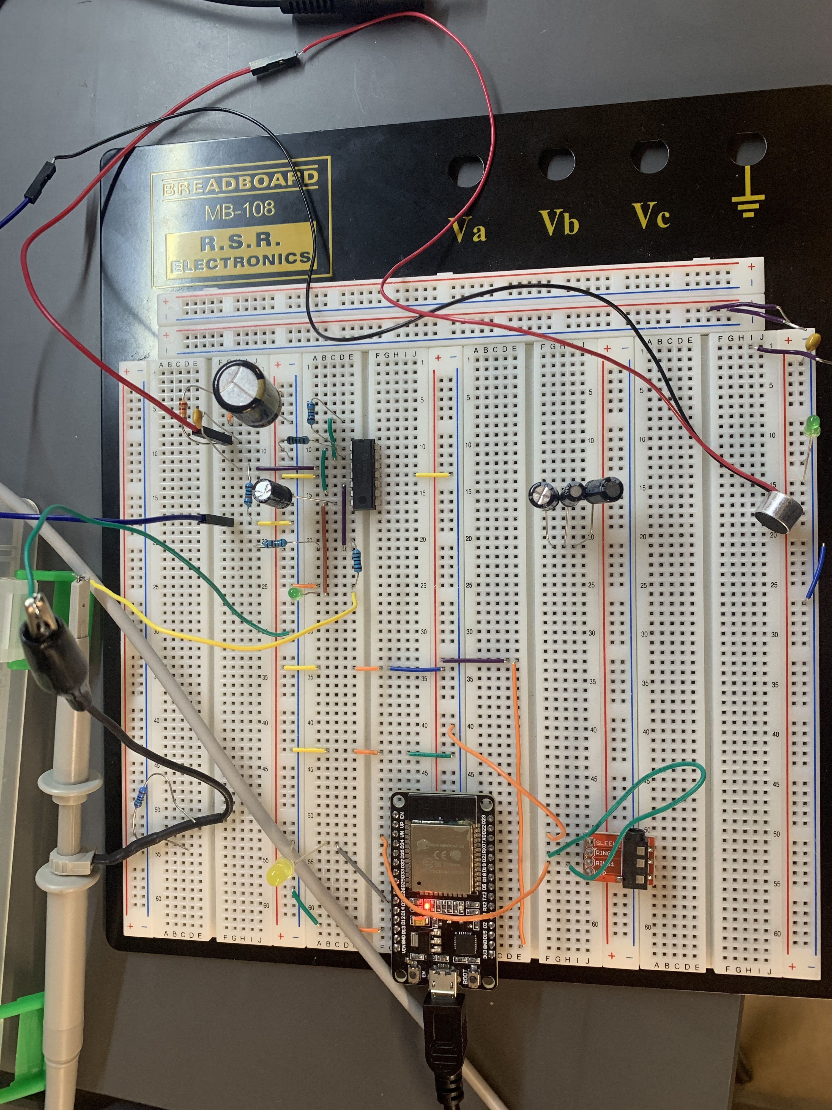
website/Team/progress/progress2pics/mic_circuit.jpg
