Avik127/RDNT/website/Team/progress/progress2pics/PCB_completed_pt2.jpg

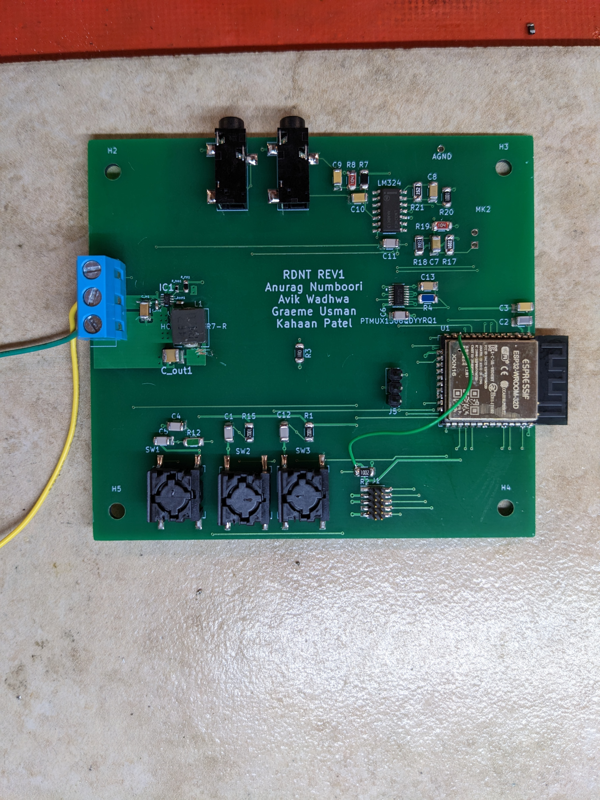
website/Team/progress/progress2pics/PCB_completed_pt2.jpg
